MillePoels/MurPhySDR/hardware/kicad/AD9364_IO.kicad_sch

## KiCad design hardware/kicad/AD9364_IO.kicad_sch (2024-05-19)

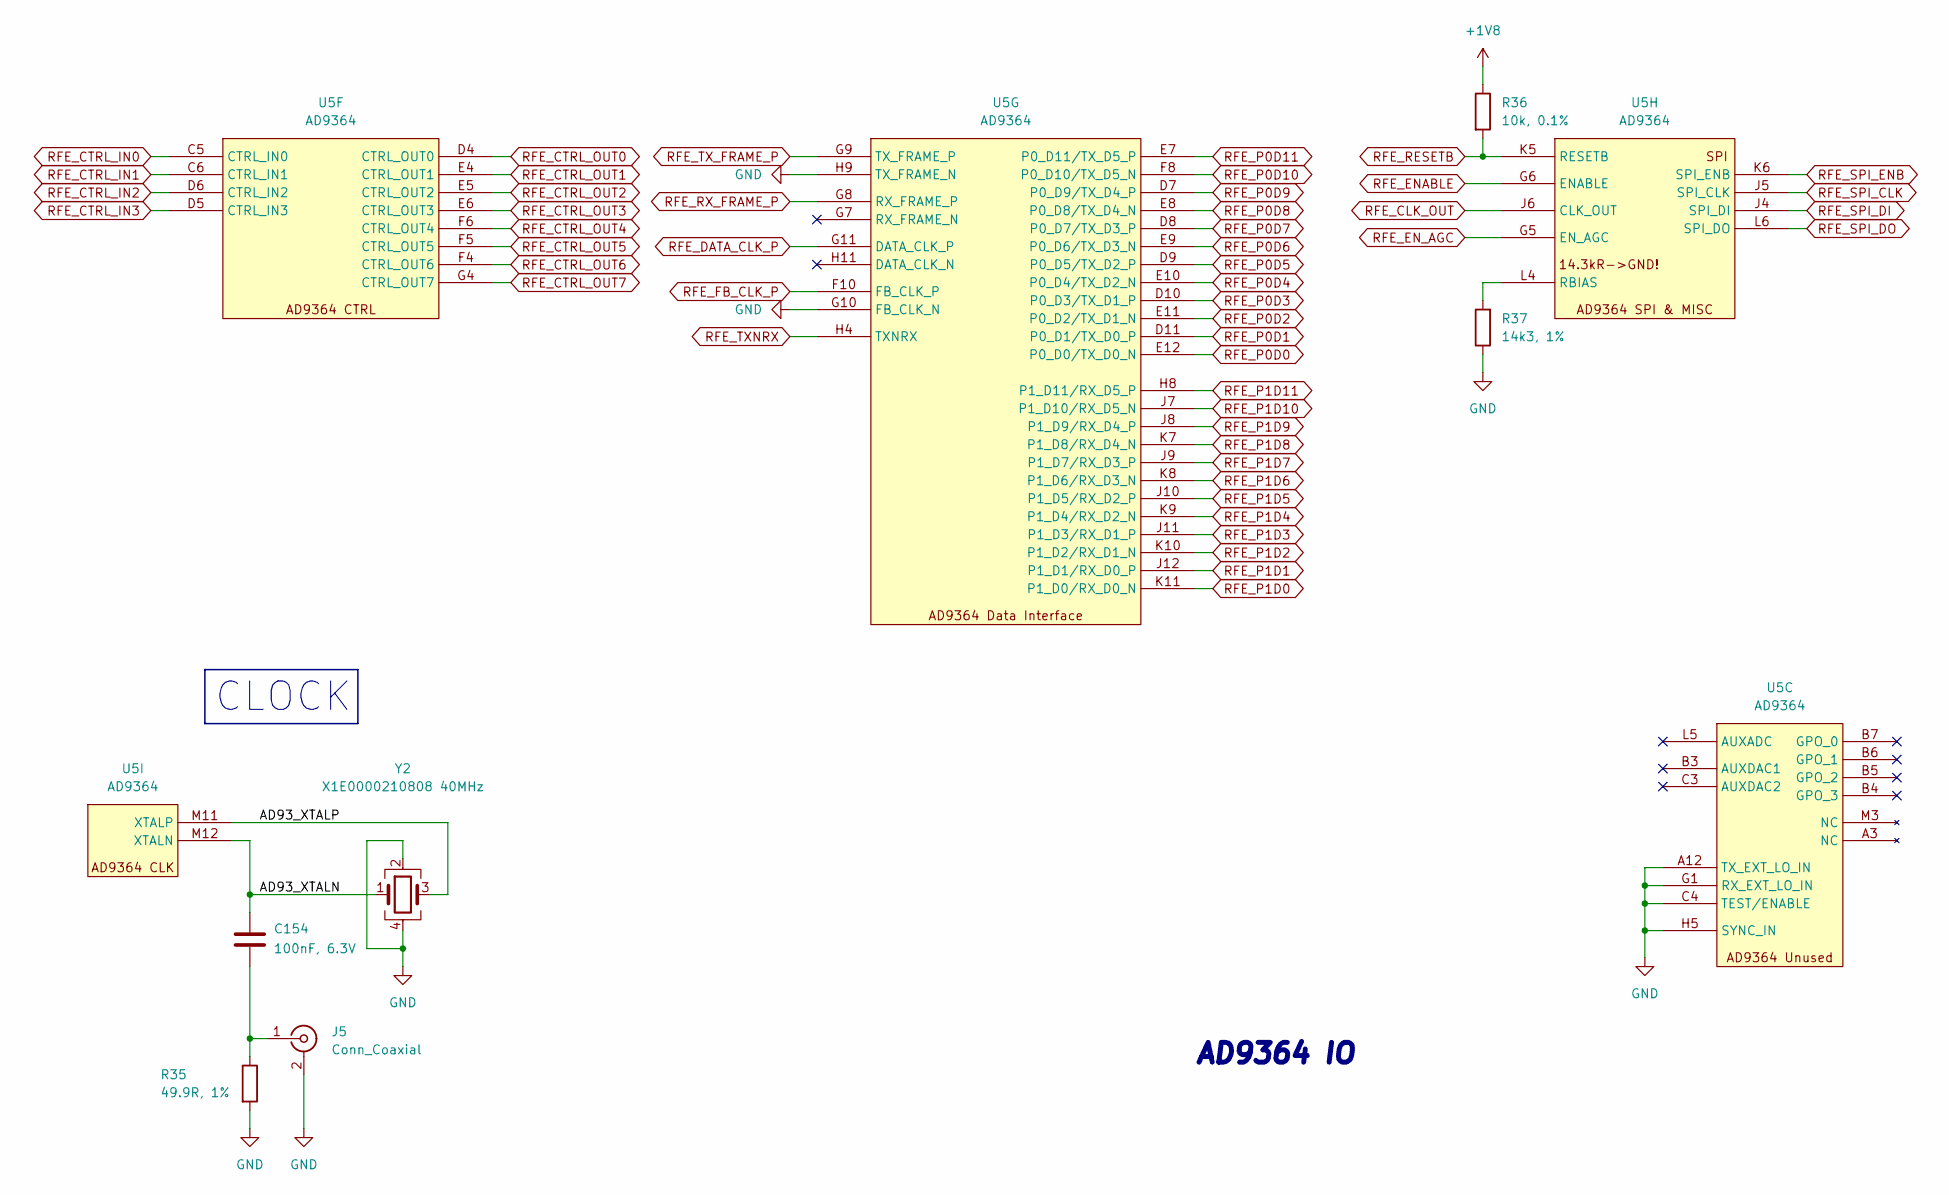
[picture p35: schematic AD9364_IO.kicad_sch]

Parts:
C154: 100nF, 6.3V; C_0201_0603Metric; Manufacturer_Part_Number GRM033R60J104KE19D; Mouser Part Number 81-GRM033R60J104KE19
J5: Conn_Coaxial; SMA_Molex_73251-1153_EdgeMount_Horizontal; Manufacturer_Part_Number 0732511150; Mouser Part Number 538-73251-1150
R35: 49.9R, 1%; R_0402_1005Metric; Manufacturer_Part_Number RC0402FR-0749R9L; Mouser Part Number 603-RC0402FR-0749R9L
R36: 10k, 0.1%; R_0402_1005Metric; Manufacturer_Part_Number RT0402BRD0710KL; Mouser Part Number 603-RT0402BRD0710KL
R37: 14k3, 1%; R_0402_1005Metric; Manufacturer_Part_Number RC0402FR-0714K3L; Mouser Part Number 603-RC0402FR-0714K3L
U5: AD9364; Manufacturer_Part_Number AD9364BBCZ; Mouser Part Number 584-AD9364BBCZ
Y2: X1E0000210808 40MHz; Crystal_SMD_SeikoEpson_TSX3225-4Pin_3.2x2.5mm; Manufacturer_Part_Number X1E0000210808; Mouser Part Number /

Connections:
+1V8: R36.1
AD93_XTALN: C154.1, U5.M12 (XTALN), Y2.1
AD93_XTALP: U5.M11 (XTALP), Y2.3
GND: J5.2 (Ext), R35.2, R37.1, U5.A12 (TX_EXT_LO_IN), U5.C4 (TEST/ENABLE), U5.G1 (RX_EXT_LO_IN), U5.G10 (FB_CLK_N), U5.H5 (SYNC_IN), U5.H9 (TX_FRAME_N), Y2.2, Y2.4
unnamed: C154.2, J5.1 (In), R35.1
unnamed: R37.2, U5.L4 (RBIAS)
RFE_CLK_OUT: U5.J6 (CLK_OUT)
RFE_CTRL_IN0: U5.C5 (CTRL_IN0)
RFE_CTRL_IN1: U5.C6 (CTRL_IN1)
RFE_CTRL_IN2: U5.D6 (CTRL_IN2)
RFE_CTRL_IN3: U5.D5 (CTRL_IN3)
RFE_CTRL_OUT0: U5.D4 (CTRL_OUT0)
RFE_CTRL_OUT1: U5.E4 (CTRL_OUT1)
RFE_CTRL_OUT2: U5.E5 (CTRL_OUT2)
RFE_CTRL_OUT3: U5.E6 (CTRL_OUT3)
RFE_CTRL_OUT4: U5.F6 (CTRL_OUT4)
RFE_CTRL_OUT5: U5.F5 (CTRL_OUT5)
RFE_CTRL_OUT6: U5.F4 (CTRL_OUT6)
RFE_CTRL_OUT7: U5.G4 (CTRL_OUT7)
RFE_DATA_CLK_P: U5.G11 (DATA_CLK_P)
RFE_ENABLE: U5.G6 (ENABLE)
RFE_EN_AGC: U5.G5 (EN_AGC)
RFE_FB_CLK_P: U5.F10 (FB_CLK_P)
RFE_P0D0: U5.E12 (P0_D0/TX_D0_N)
RFE_P0D1: U5.D11 (P0_D1/TX_D0_P)
RFE_P0D2: U5.E11 (P0_D2/TX_D1_N)
RFE_P0D3: U5.D10 (P0_D3/TX_D1_P)
RFE_P0D4: U5.E10 (P0_D4/TX_D2_N)
RFE_P0D5: U5.D9 (P0_D5/TX_D2_P)
RFE_P0D6: U5.E9 (P0_D6/TX_D3_N)
RFE_P0D7: U5.D8 (P0_D7/TX_D3_P)
RFE_P0D8: U5.E8 (P0_D8/TX_D4_N)
RFE_P0D9: U5.D7 (P0_D9/TX_D4_P)
RFE_P0D10: U5.F8 (P0_D10/TX_D5_N)
RFE_P0D11: U5.E7 (P0_D11/TX_D5_P)
RFE_P1D0: U5.K11 (P1_D0/RX_D0_N)
RFE_P1D1: U5.J12 (P1_D1/RX_D0_P)
RFE_P1D2: U5.K10 (P1_D2/RX_D1_N)
RFE_P1D3: U5.J11 (P1_D3/RX_D1_P)
RFE_P1D4: U5.K9 (P1_D4/RX_D2_N)
RFE_P1D5: U5.J10 (P1_D5/RX_D2_P)
RFE_P1D6: U5.K8 (P1_D6/RX_D3_N)
RFE_P1D7: U5.J9 (P1_D7/RX_D3_P)
RFE_P1D8: U5.K7 (P1_D8/RX_D4_N)
RFE_P1D9: U5.J8 (P1_D9/RX_D4_P)
RFE_P1D10: U5.J7 (P1_D10/RX_D5_N)
RFE_P1D11: U5.H8 (P1_D11/RX_D5_P)
RFE_RESETB: R36.2, U5.K5 (RESETB)
RFE_RX_FRAME_P: U5.G8 (RX_FRAME_P)
RFE_SPI_CLK: U5.J5 (SPI_CLK)
RFE_SPI_DI: U5.J4 (SPI_DI)
RFE_SPI_DO: U5.L6 (SPI_DO)
RFE_SPI_ENB: U5.K6 (SPI_ENB)
RFE_TXNRX: U5.H4 (TXNRX)
RFE_TX_FRAME_P: U5.G9 (TX_FRAME_P)

Notes on the sheet:
AD9364 IO
CLOCK
