MillePoels/MurPhySDR/hardware/kicad/AD9364_RF.kicad_sch

## KiCad design hardware/kicad/AD9364_RF.kicad_sch (2024-05-19)

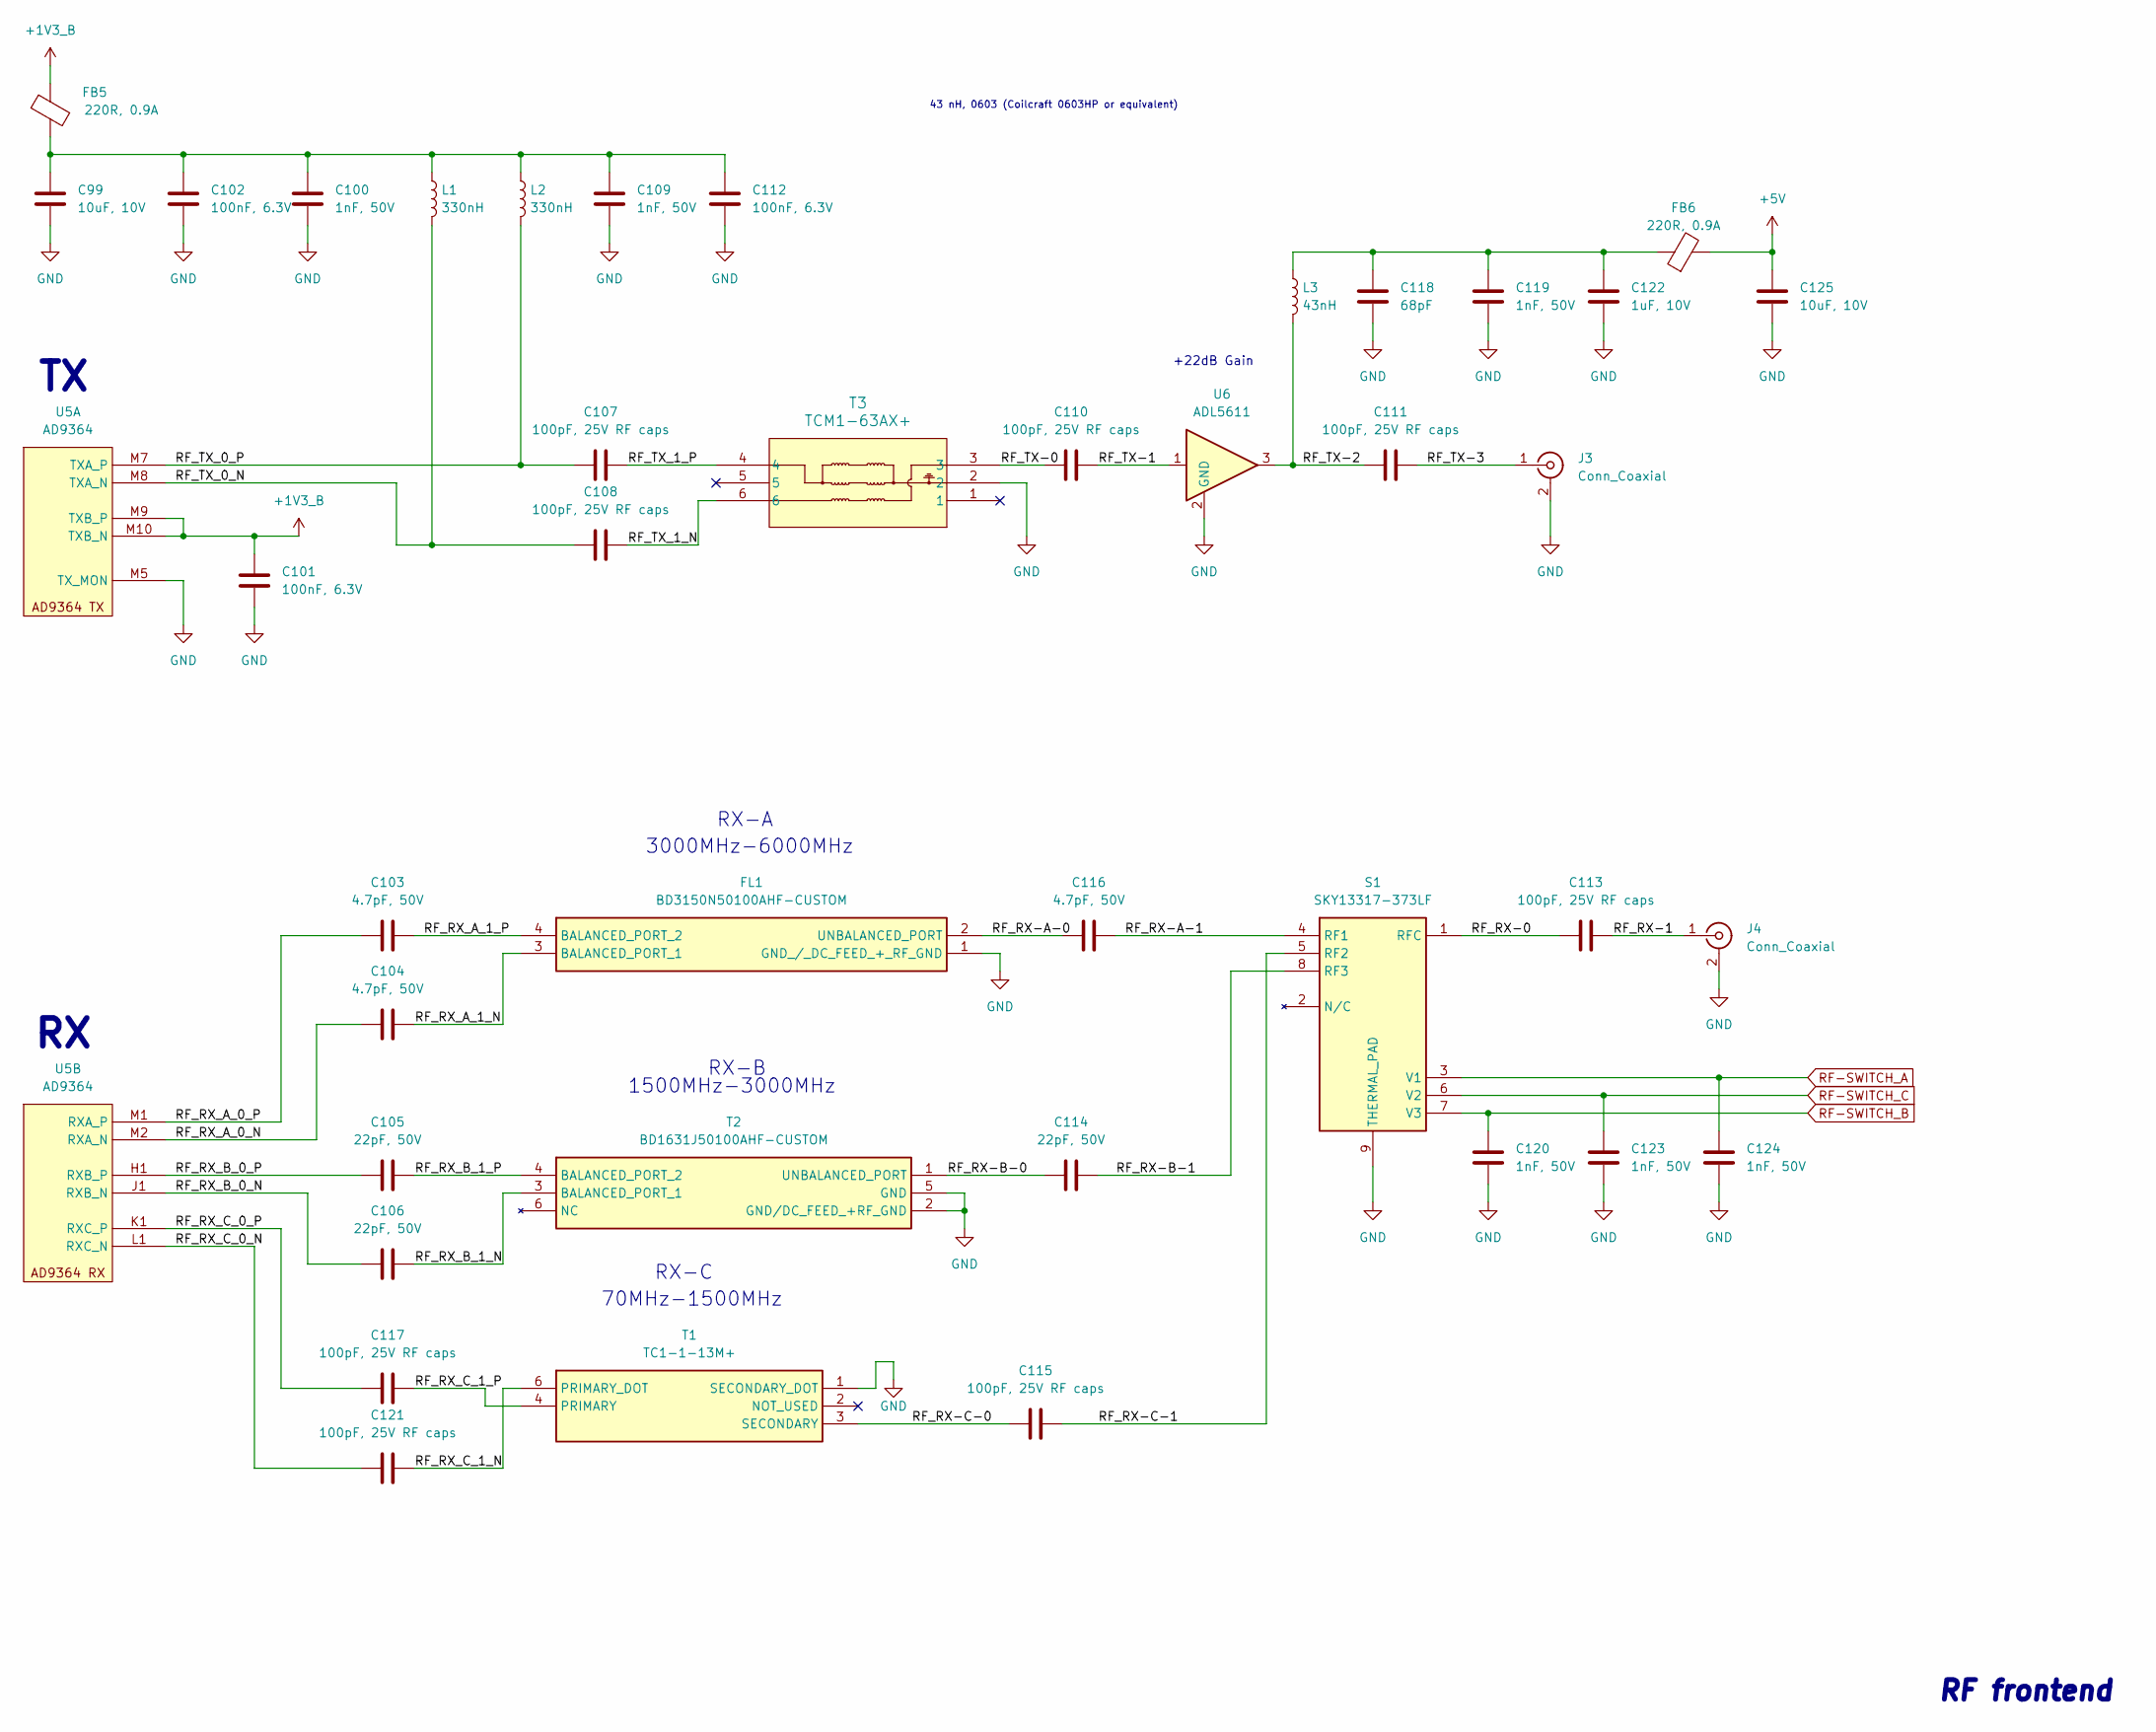
[picture p36: schematic AD9364_RF.kicad_sch]

Parts:
C99, C125: 10uF, 10V; C_0603_1608Metric; Manufacturer_Part_Number GRM188R61A106ME69D; Mouser Part Number 81-GRM188R61A106ME9D
C100, C109, C119, C120, C123, C124: 1nF, 50V; C_0201_0603Metric; Manufacturer_Part_Number GRM0335C1H102JE01D; Mouser Part Number 81-GRM0335C1H102JE1D
C101, C102, C112: 100nF, 6.3V; C_0201_0603Metric; Manufacturer_Part_Number GRM033R60J104KE19D; Mouser Part Number 81-GRM033R60J104KE19
C103, C104, C116: 4.7pF, 50V; C_0201_0603Metric; Manufacturer_Part_Number GRM0335C1H4R7BA01D; Mouser Part Number 81-GRM0335C1H4R7BA1D
C105, C106, C114: 22pF, 50V; C_0201_0603Metric; Manufacturer_Part_Number GRM0335C1H220JA01D; Mouser Part Number 81-GRM0335C1H220JA1D
C107, C108, C110, C111, C113, C115, C117, C121: 100pF, 25V RF caps; C_0402_1005Metric; Manufacturer_Part_Number CBR04C101G3GAC; Mouser Part Number 80-CBR04C101G3GAC
C118: 68pF; C_0402_1005Metric; Manufacturer_Part_Number CC0402JRNPO9BN680; Mouser Part Number 603-CC402JRNPO9BN680
C122: 1uF, 10V; C_0402_1005Metric; Manufacturer_Part_Number GRM155Z71A105KE01D; Mouser Part Number 81-GRM155Z71A105KE1D
FB5, FB6: 220R, 0.9A; L_0402_1005Metric; Manufacturer_Part_Number MPZ1005S221ET000; Mouser Part Number 810-MPZ1005S221ET000
FL1: BD3150N50100AHF-CUSTOM; BD3150N50100AHF; Mouser Part Number 620-BD3150N50100AHF
J3, J4: Conn_Coaxial; SMA_Molex_73251-1153_EdgeMount_Horizontal; Manufacturer_Part_Number 0732511150; Mouser Part Number 538-73251-1150
L1, L2: 330nH; L_0402_1005Metric; Manufacturer_Part_Number LQW15CNR33J1ZD; Mouser Part Number 81-LQW15CNR33J1ZD
L3: 43nH; L_0603_1608Metric; Manufacturer_Part_Number LQW18AN43NG00D; Mouser Part Number 81-LQW18AN43NG00D
S1: SKY13317-373LF; SON40P155X155X50-9N_(SKY13317-373LF); Mouser Part Number 873-SKY13317-373LF
T1: TC1-1-13M+; TC1113MA; Mouser Part Number 139-TC1-1-13MA
T2: BD1631J50100AHF-CUSTOM; BD1631J50100AHF; Mouser Part Number 620-BD1631J50100AHF
T3: TCM1-63AX+; Manufacturer_Part_Number TCM1-63AX+; Mouser Part Number 139-TCM1-63AX
U5: AD9364; Manufacturer_Part_Number AD9364BBCZ; Mouser Part Number 584-AD9364BBCZ
U6: ADL5611; SOT-89-3; Manufacturer_Part_Number ADL5611ARKZ-R7; Mouser Part Number ADL5611ARKZ-R7

Connections:
+1V3_B: C101.1, FB5.2, U5.M9 (TXB_P), U5.M10 (TXB_N)
+5V: C125.1, FB6.2
GND: C99.2, C100.2, C101.2, C102.2, C109.2, C112.2, C118.2, C119.2, C120.2, C122.1, C123.2, C124.2, C125.2, FL1.1 (GND_/_DC_FEED_+_RF_GND), J3.2 (Ext), J4.2 (Ext), S1.9 (THERMAL_PAD), T1.1 (SECONDARY_DOT), T2.2 (GND/DC_FEED_+RF_GND), T2.5 (GND), T3.2, U5.M5 (TX_MON), U6.2 (GND)
unnamed: C99.1, C100.1, C102.1, C109.1, C112.1, FB5.1, L1.1, L2.1
unnamed: C118.1, C119.1, C122.2, FB6.1, L3.1
RF-SWITCH_A: C124.1, S1.3 (V1)
RF-SWITCH_B: C120.1, S1.7 (V3)
RF-SWITCH_C: C123.1, S1.6 (V2)
RF_RX-0: C113.1, S1.1 (RFC)
RF_RX-1: C113.2, J4.1 (In)
RF_RX-A-0: C116.1, FL1.2 (UNBALANCED_PORT)
RF_RX-A-1: C116.2, S1.4 (RF1)
RF_RX-B-0: C114.1, T2.1 (UNBALANCED_PORT)
RF_RX-B-1: C114.2, S1.8 (RF3)
RF_RX-C-0: C115.1, T1.3 (SECONDARY)
RF_RX-C-1: C115.2, S1.5 (RF2)
RF_RX_A_0_N: C104.1, U5.M2 (RXA_N)
RF_RX_A_0_P: C103.1, U5.M1 (RXA_P)
RF_RX_A_1_N: C104.2, FL1.3 (BALANCED_PORT_1)
RF_RX_A_1_P: C103.2, FL1.4 (BALANCED_PORT_2)
RF_RX_B_0_N: C106.1, U5.J1 (RXB_N)
RF_RX_B_0_P: C105.1, U5.H1 (RXB_P)
RF_RX_B_1_N: C106.2, T2.3 (BALANCED_PORT_1)
RF_RX_B_1_P: C105.2, T2.4 (BALANCED_PORT_2)
RF_RX_C_0_N: C121.1, U5.L1 (RXC_N)
RF_RX_C_0_P: C117.1, U5.K1 (RXC_P)
RF_RX_C_1_N: C121.2, T1.6 (PRIMARY_DOT)
RF_RX_C_1_P: C117.2, T1.4 (PRIMARY)
RF_TX-0: C110.1, T3.3
RF_TX-1: C110.2, U6.1
RF_TX-2: C111.1, L3.2, U6.3
RF_TX-3: C111.2, J3.1 (In)
RF_TX_0_N: C108.1, L1.2, U5.M8 (TXA_N)
RF_TX_0_P: C107.1, L2.2, U5.M7 (TXA_P)
RF_TX_1_N: C108.2, T3.6
RF_TX_1_P: C107.2, T3.4

Notes on the sheet:
43 nH, 0603 (Coilcraft 0603HP or equivalent)
RF frontend
RX-C
+22dB Gain
3000MHz-6000MHz
1500MHz-3000MHz
RX-B
RX-A
70MHz-1500MHz
