MillePoels/MurPhySDR/hardware/kicad/AD9364_power-supply.kicad_sch

## KiCad design hardware/kicad/AD9364_power-supply.kicad_sch (2024-05-19)

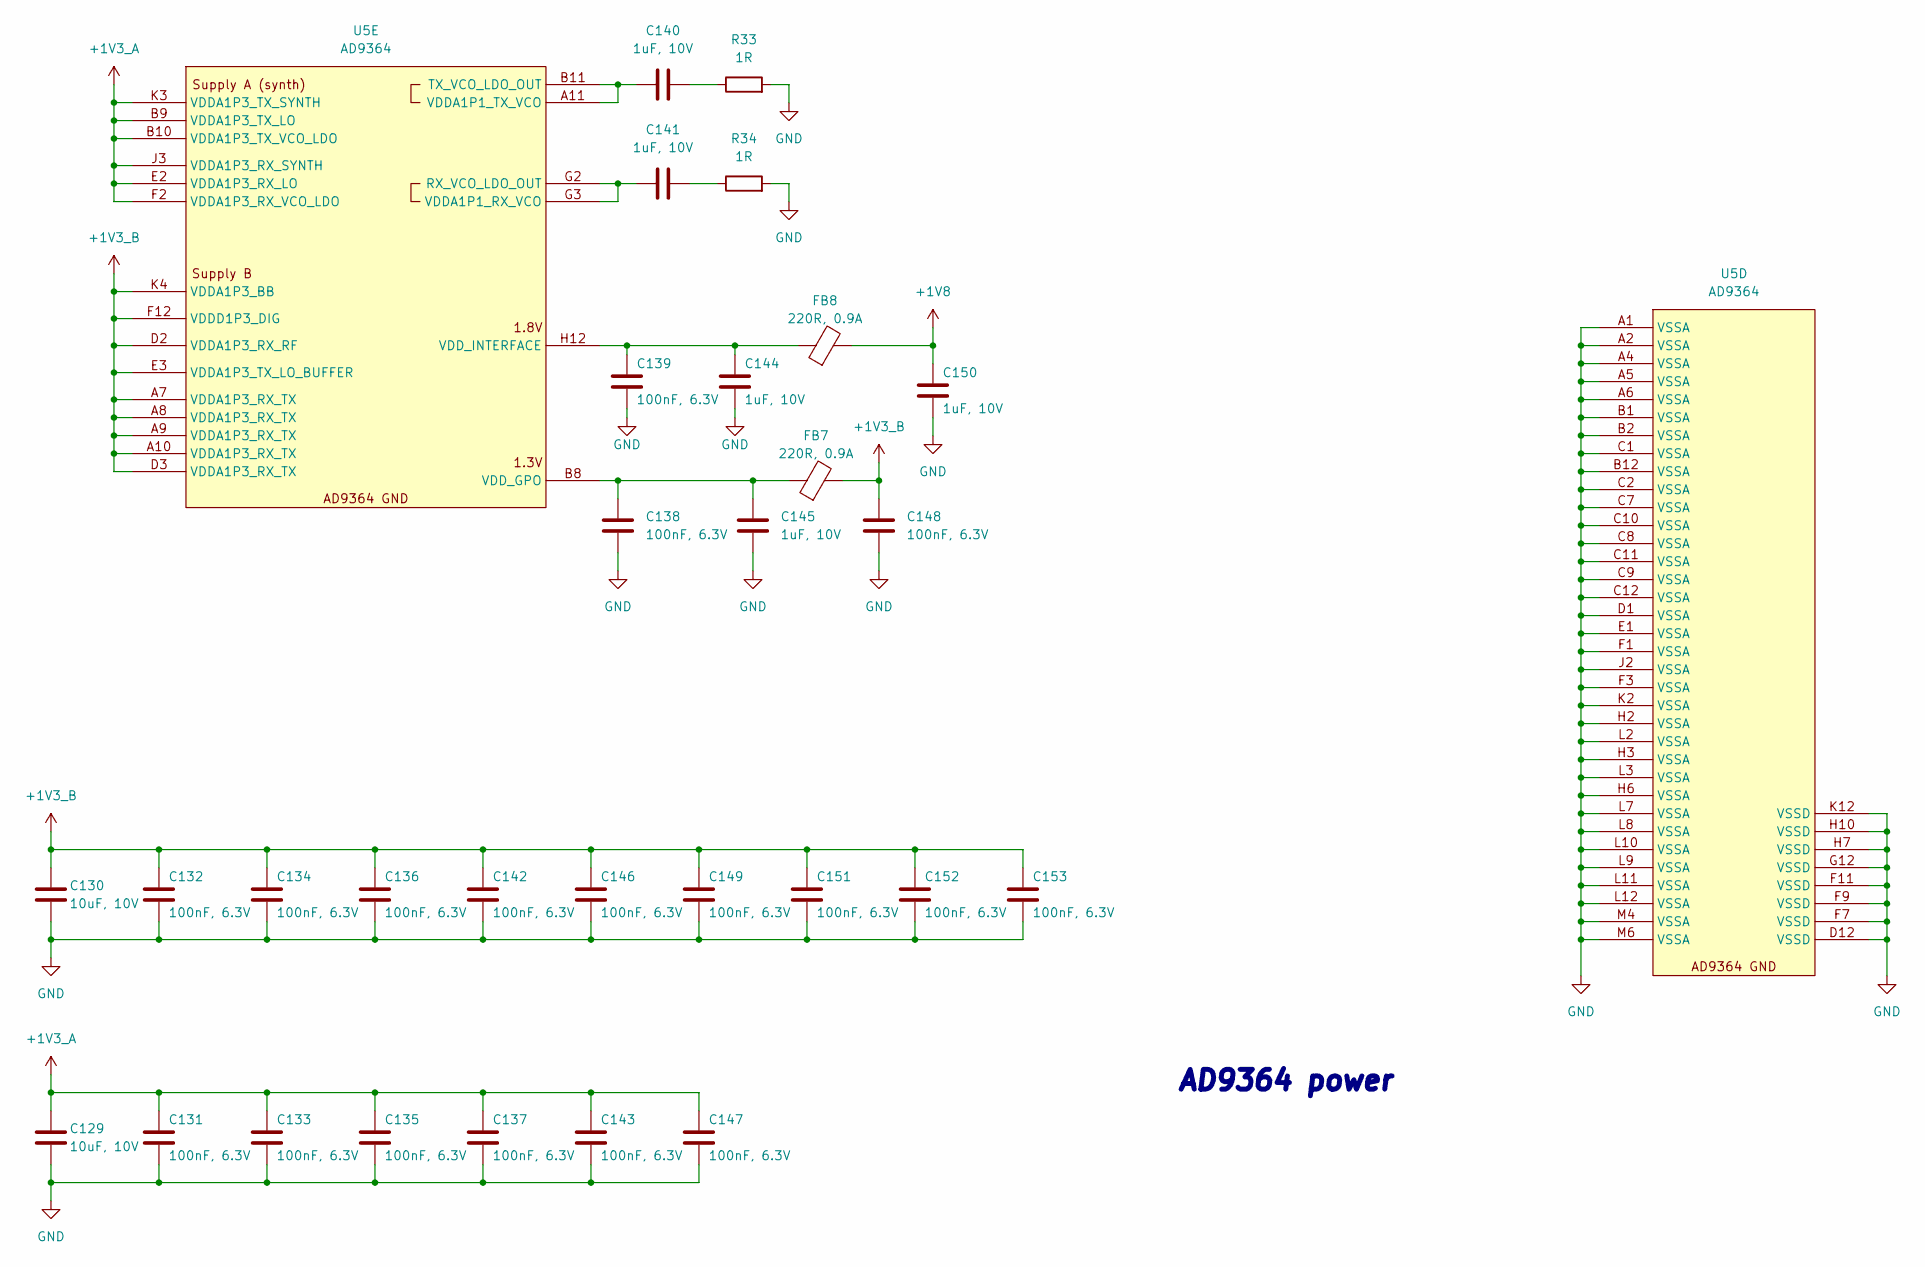
[picture p37: schematic AD9364_power-supply.kicad_sch]

Parts:
C129, C130: 10uF, 10V; C_0603_1608Metric; Manufacturer_Part_Number GRM188R61A106ME69D; Mouser Part Number 81-GRM188R61A106ME9D
C131, C132, C133, C134, C135, C136, C137, C138, C139, C142, C143, C146, C147, C148, C149, C151, C152, C153: 100nF, 6.3V; C_0201_0603Metric; Manufacturer_Part_Number GRM033R60J104KE19D; Mouser Part Number 81-GRM033R60J104KE19
C140, C141, C144, C145, C150: 1uF, 10V; C_0402_1005Metric; Manufacturer_Part_Number GRM155Z71A105KE01D; Mouser Part Number 81-GRM155Z71A105KE1D
FB7, FB8: 220R, 0.9A; L_0402_1005Metric; Manufacturer_Part_Number MPZ1005S221ET000; Mouser Part Number 810-MPZ1005S221ET000
R33, R34: 1R; R_0402_1005Metric; Manufacturer_Part_Number RC0402FR-071RL; Mouser Part Number 603-RC0402FR-071RL
U5: AD9364; Manufacturer_Part_Number AD9364BBCZ; Mouser Part Number 584-AD9364BBCZ

Connections:
+1V3_A: C129.1, C131.1, C133.1, C135.1, C137.1, C143.1, C147.1, U5.B9 (VDDA1P3_TX_LO), U5.B10 (VDDA1P3_TX_VCO_LDO), U5.E2 (VDDA1P3_RX_LO), U5.F2 (VDDA1P3_RX_VCO_LDO), U5.J3 (VDDA1P3_RX_SYNTH), U5.K3 (VDDA1P3_TX_SYNTH)
+1V3_B: C130.1, C132.1, C134.1, C136.1, C142.1, C146.1, C148.1, C149.1, C151.1, C152.1, C153.1, FB7.2, U5.A7 (VDDA1P3_RX_TX), U5.A8 (VDDA1P3_RX_TX), U5.A9 (VDDA1P3_RX_TX), U5.A10 (VDDA1P3_RX_TX), U5.D2 (VDDA1P3_RX_RF), U5.D3 (VDDA1P3_RX_TX), U5.E3 (VDDA1P3_TX_LO_BUFFER), U5.F12 (VDDD1P3_DIG), U5.K4 (VDDA1P3_BB)
+1V8: C150.1, FB8.2
GND: C129.2, C130.2, C131.2, C132.2, C133.2, C134.2, C135.2, C136.2, C137.2, C138.2, C139.2, C142.2, C143.2, C144.2, C145.2, C146.2, C147.2, C148.2, C149.2, C150.2, C151.2, C152.2, C153.2, R33.2, R34.2, U5.A1 (VSSA), U5.A2 (VSSA), U5.A4 (VSSA), U5.A5 (VSSA), U5.A6 (VSSA), U5.B1 (VSSA), U5.B2 (VSSA), U5.B12 (VSSA), U5.C1 (VSSA), U5.C2 (VSSA), U5.C7 (VSSA), U5.C8 (VSSA), U5.C9 (VSSA), U5.C10 (VSSA), U5.C11 (VSSA), U5.C12 (VSSA), U5.D1 (VSSA), U5.D12 (VSSD), U5.E1 (VSSA), U5.F1 (VSSA), U5.F3 (VSSA), U5.F7 (VSSD), U5.F9 (VSSD), U5.F11 (VSSD), U5.G12 (VSSD), U5.H2 (VSSA), U5.H3 (VSSA), U5.H6 (VSSA), U5.H7 (VSSD), U5.H10 (VSSD), U5.J2 (VSSA), U5.K2 (VSSA), U5.K12 (VSSD), U5.L2 (VSSA), U5.L3 (VSSA), U5.L7 (VSSA), U5.L8 (VSSA), U5.L9 (VSSA), U5.L10 (VSSA), U5.L11 (VSSA), U5.L12 (VSSA), U5.M4 (VSSA), U5.M6 (VSSA)
unnamed: C138.1, C145.1, FB7.1, U5.B8 (VDD_GPO)
unnamed: C139.1, C144.1, FB8.1, U5.H12 (VDD_INTERFACE)
unnamed: C140.1, R33.1
unnamed: C140.2, U5.A11 (VDDA1P1_TX_VCO), U5.B11 (TX_VCO_LDO_OUT)
unnamed: C141.1, R34.1
unnamed: C141.2, U5.G2 (RX_VCO_LDO_OUT), U5.G3 (VDDA1P1_RX_VCO)

Notes on the sheet:
AD9364 power
