MillePoels/MurPhySDR/hardware/kicad/FT601Q.kicad_sch

## KiCad design hardware/kicad/FT601Q.kicad_sch (2024-05-19)

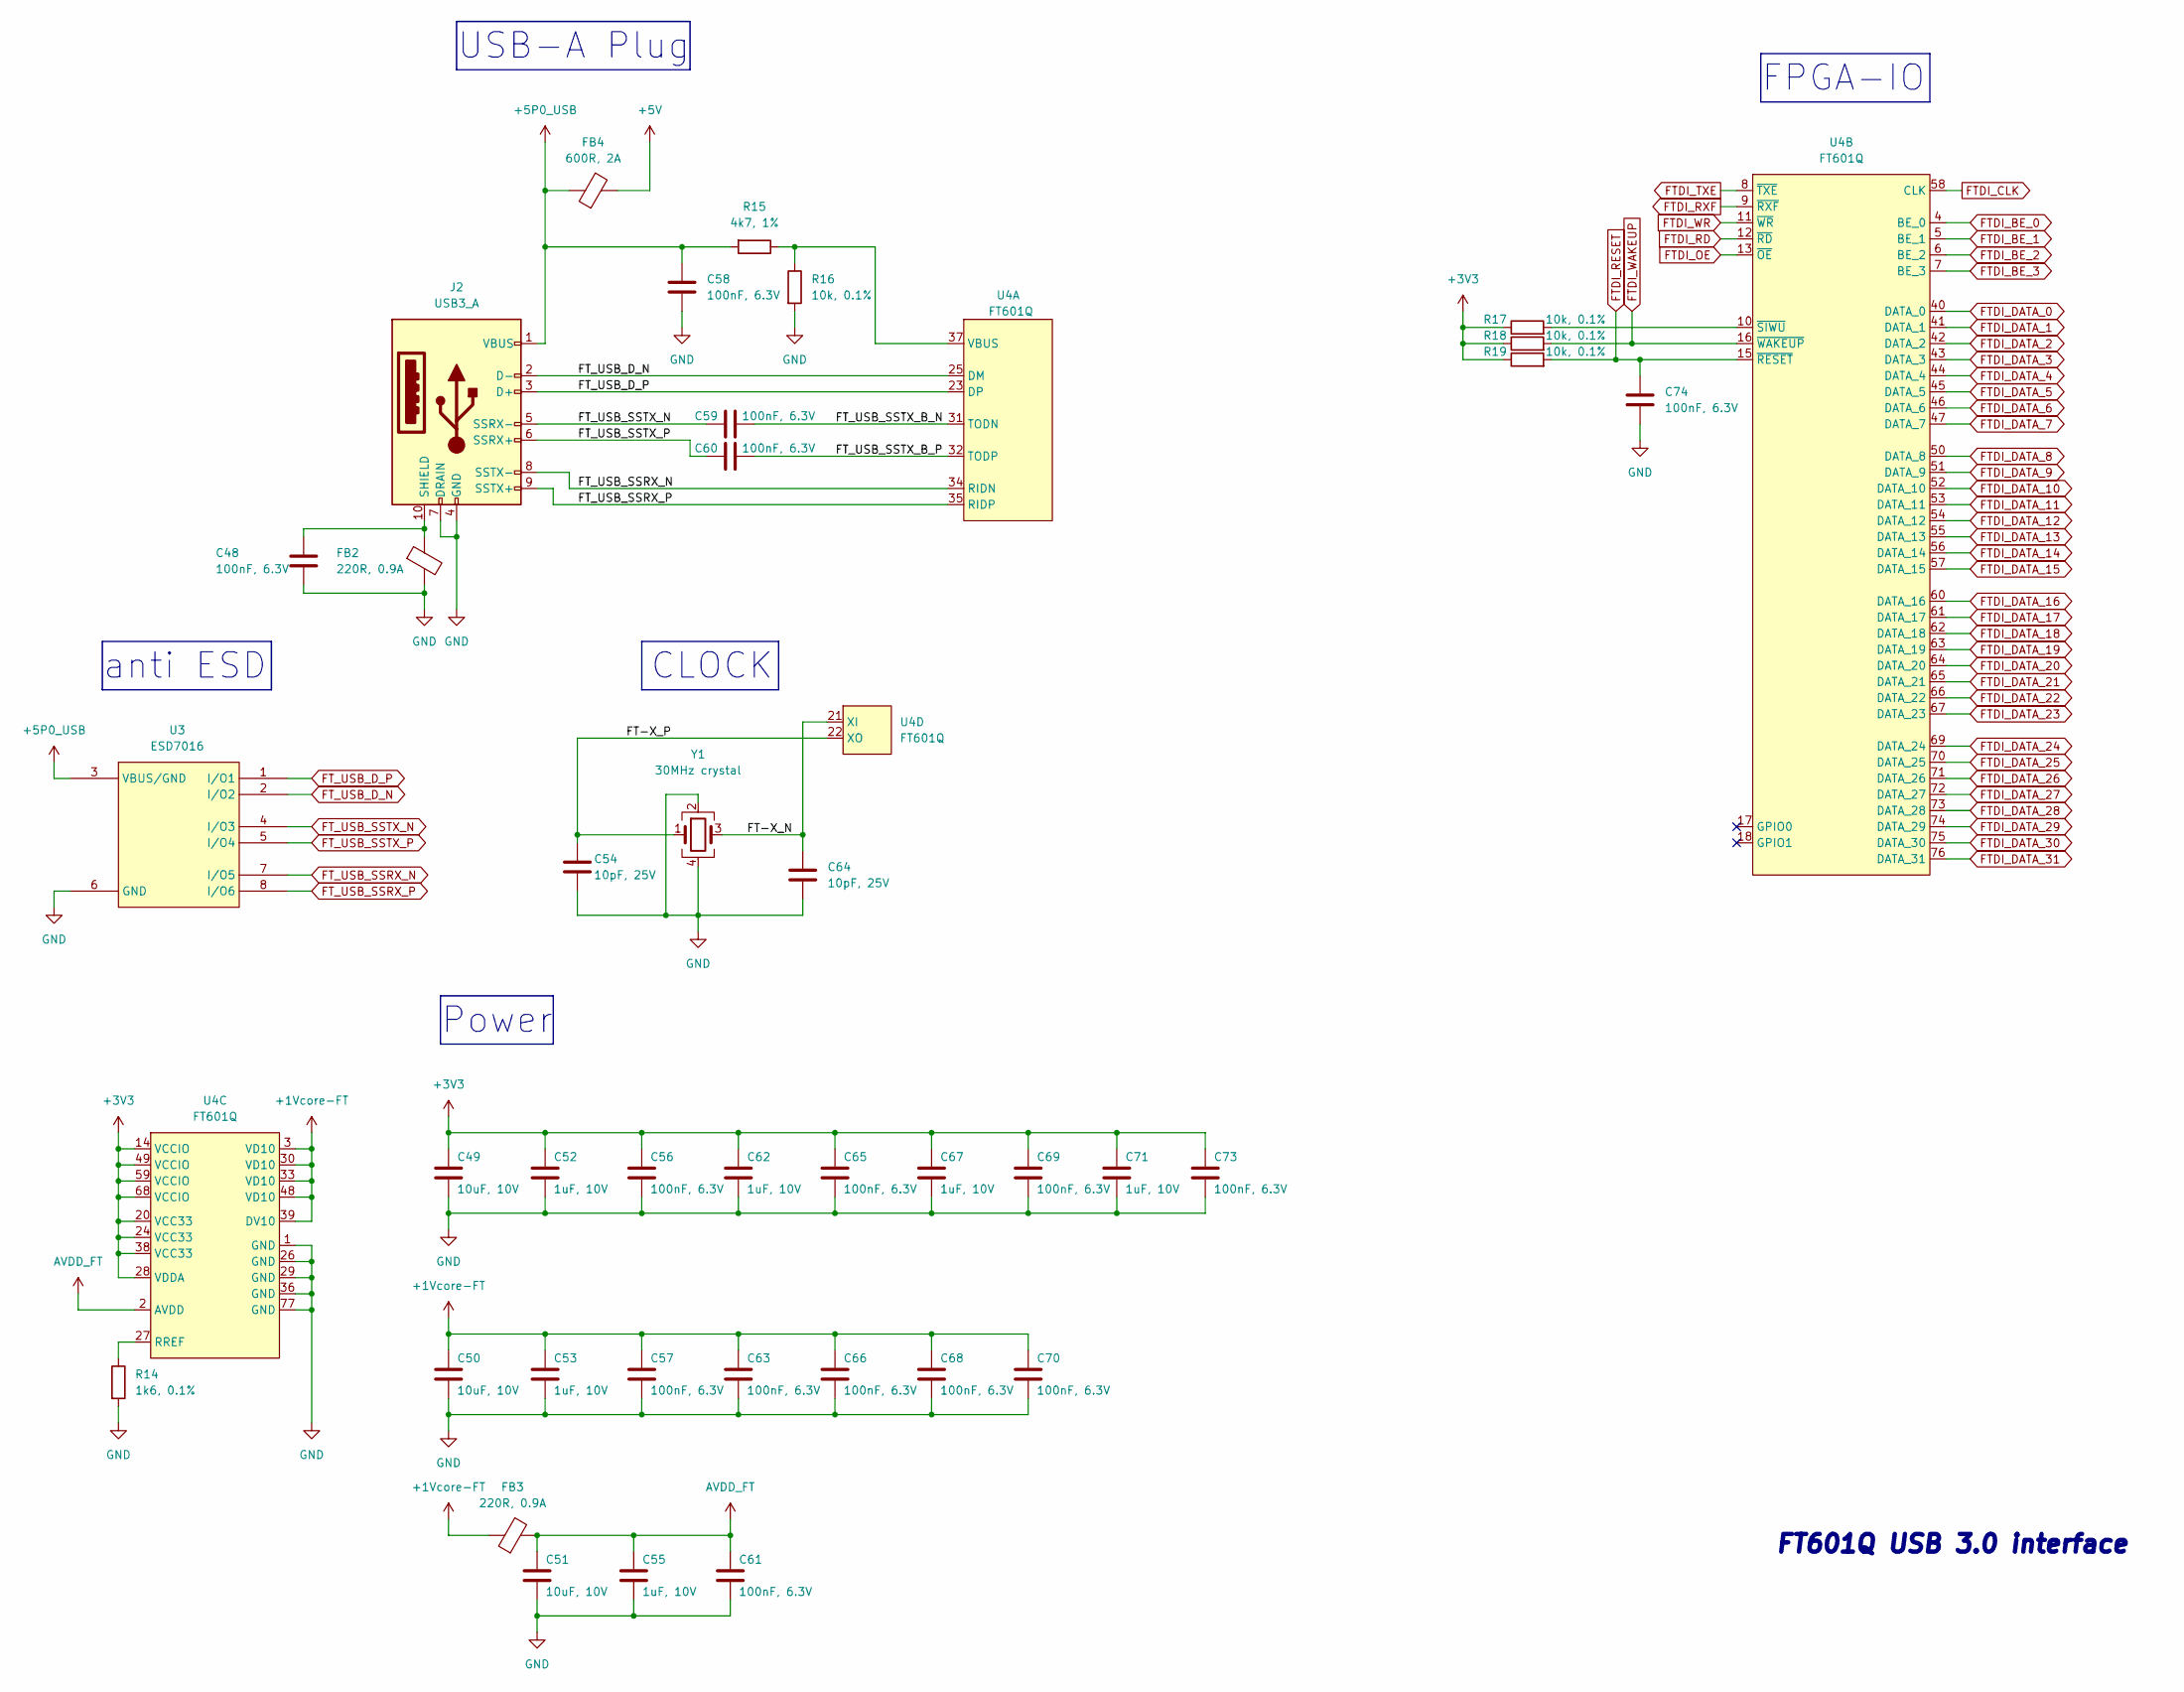
[picture p38: schematic FT601Q.kicad_sch]

Parts:
C48, C56, C57, C58, C59, C60, C61, C63, C65, C66, C68, C69, C70, C73, C74: 100nF, 6.3V; C_0201_0603Metric; Manufacturer_Part_Number GRM033R60J104KE19D; Mouser Part Number 81-GRM033R60J104KE19
C49, C50, C51: 10uF, 10V; C_0603_1608Metric; Manufacturer_Part_Number GRM188R61A106ME69D; Mouser Part Number 81-GRM188R61A106ME9D
C52, C53, C55, C62, C67, C71: 1uF, 10V; C_0402_1005Metric; Manufacturer_Part_Number GRM155Z71A105KE01D; Mouser Part Number 81-GRM155Z71A105KE1D
C54, C64: 10pF, 25V; C_0402_1005Metric; Manufacturer_Part_Number GRM1555C1E100JA01D; Mouser Part Number 81-GRM1555C1E100JA1D
FB2, FB3: 220R, 0.9A; L_0402_1005Metric; Manufacturer_Part_Number MPZ1005S221ET000; Mouser Part Number 810-MPZ1005S221ET000
FB4: 600R, 2A; L_0805_2012Metric; Manufacturer_Part_Number MPZ2012S601AT000; Mouser Part Number 810-MPZ2012S601AT000
J2: USB3_A; USB3.0-A-SMD_U237-091N-4BLVS10-1; Manufacturer_Part_Number U237-091N-4BLVS10-1; Mouser Part Number /
R14: 1k6, 0.1%; R_0402_1005Metric; Manufacturer_Part_Number RT0402BRD071K6L; Mouser Part Number 603-RT0402BRD071K6L
R15: 4k7, 1%; R_0402_1005Metric; Manufacturer_Part_Number RC0402FR-074K7L; Mouser Part Number 603-RC0402FR-074K7L
R16, R17, R18, R19: 10k, 0.1%; R_0402_1005Metric; Manufacturer_Part_Number RT0402BRD0710KL; Mouser Part Number 603-RT0402BRD0710KL
U3: ESD7016; UDFN8_3P3X1_517CB_ONS; Manufacturer_Part_Number ESD7016MUTAG; Mouser Part Number 863-ESD7016MUTAG
U4: FT601Q; QFN-76-1EP_9x9mm_P0.4mm_EP5.81x6.31mm; Manufacturer_Part_Number FT601Q-B-T; Mouser Part Number 895-FT601Q-B-T
Y1: 30MHz crystal; Crystal_SMD_3225-4Pin_3.2x2.5mm; Manufacturer_Part_Number CX3225SB30000D0FPLCC; Mouser Part Number 581-CX3225SB3DFPLCC

Connections:
+1Vcore-FT: C50.1, C53.1, C57.1, C63.1, C66.1, C68.1, C70.1, FB3.1, U4.3 (VD10), U4.30 (VD10), U4.33 (VD10), U4.39 (DV10), U4.48 (VD10)
+3V3: C49.1, C52.1, C56.1, C62.1, C65.1, C67.1, C69.1, C71.1, C73.1, R17.1, R18.1, R19.1, U4.14 (VCCIO), U4.20 (VCC33), U4.24 (VCC33), U4.28 (VDDA), U4.38 (VCC33), U4.49 (VCCIO), U4.59 (VCCIO), U4.68 (VCCIO)
+5P0_USB: C58.1, FB4.1, J2.1 (VBUS), R15.2, U3.3 (VBUS/GND)
+5V: FB4.2
AVDD_FT: C51.1, C55.1, C61.1, FB3.2, U4.2 (AVDD)
FT-X_N: C64.1, U4.21 (XI), Y1.3
FT-X_P: C54.1, U4.22 (XO), Y1.1
FTDI_BE_0: U4.4 (BE_0)
FTDI_BE_1: U4.5 (BE_1)
FTDI_BE_2: U4.6 (BE_2)
FTDI_BE_3: U4.7 (BE_3)
FTDI_CLK: U4.58 (CLK)
FTDI_DATA_0: U4.40 (DATA_0)
FTDI_DATA_1: U4.41 (DATA_1)
FTDI_DATA_2: U4.42 (DATA_2)
FTDI_DATA_3: U4.43 (DATA_3)
FTDI_DATA_4: U4.44 (DATA_4)
FTDI_DATA_5: U4.45 (DATA_5)
FTDI_DATA_6: U4.46 (DATA_6)
FTDI_DATA_7: U4.47 (DATA_7)
FTDI_DATA_8: U4.50 (DATA_8)
FTDI_DATA_9: U4.51 (DATA_9)
FTDI_DATA_10: U4.52 (DATA_10)
FTDI_DATA_11: U4.53 (DATA_11)
FTDI_DATA_12: U4.54 (DATA_12)
FTDI_DATA_13: U4.55 (DATA_13)
FTDI_DATA_14: U4.56 (DATA_14)
FTDI_DATA_15: U4.57 (DATA_15)
FTDI_DATA_16: U4.60 (DATA_16)
FTDI_DATA_17: U4.61 (DATA_17)
FTDI_DATA_18: U4.62 (DATA_18)
FTDI_DATA_19: U4.63 (DATA_19)
FTDI_DATA_20: U4.64 (DATA_20)
FTDI_DATA_21: U4.65 (DATA_21)
FTDI_DATA_22: U4.66 (DATA_22)
FTDI_DATA_23: U4.67 (DATA_23)
FTDI_DATA_24: U4.69 (DATA_24)
FTDI_DATA_25: U4.70 (DATA_25)
FTDI_DATA_26: U4.71 (DATA_26)
FTDI_DATA_27: U4.72 (DATA_27)
FTDI_DATA_28: U4.73 (DATA_28)
FTDI_DATA_29: U4.74 (DATA_29)
FTDI_DATA_30: U4.75 (DATA_30)
FTDI_DATA_31: U4.76 (DATA_31)
FTDI_OE: U4.13 (~OE)
FTDI_RD: U4.12 (~RD)
FTDI_RESET: C74.1, R19.2, U4.15 (~RESET)
FTDI_RXF: U4.9 (~RXF)
FTDI_TXE: U4.8 (~TXE)
FTDI_WAKEUP: R18.2, U4.16 (~WAKEUP)
FTDI_WR: U4.11 (~WR)
FT_USB_D_N: J2.2 (D-), U3.2 (I/O2), U4.25 (DM)
FT_USB_D_P: J2.3 (D+), U3.1 (I/O1), U4.23 (DP)
FT_USB_SSRX_N: J2.8 (SSTX-), U3.7 (I/O5), U4.34 (RIDN)
FT_USB_SSRX_P: J2.9 (SSTX+), U3.8 (I/O6), U4.35 (RIDP)
FT_USB_SSTX_B_N: C59.2, U4.31 (TODN)
FT_USB_SSTX_B_P: C60.2, U4.32 (TODP)
FT_USB_SSTX_N: C59.1, J2.5 (SSRX-), U3.4 (I/O3)
FT_USB_SSTX_P: C60.1, J2.6 (SSRX+), U3.5 (I/O4)
GND: C48.2, C49.2, C50.2, C51.2, C52.2, C53.2, C54.2, C55.2, C56.2, C57.2, C58.2, C61.2, C62.2, C63.2, C64.2, C65.2, C66.2, C67.2, C68.2, C69.2, C70.2, C71.2, C73.2, C74.2, FB2.2, J2.4 (GND), J2.7 (DRAIN), R14.2, R16.2, U3.6 (GND), U4.1 (GND), U4.26 (GND), U4.29 (GND), U4.36 (GND), U4.77 (GND), Y1.2, Y1.4
unnamed: C48.1, FB2.1, J2.10 (SHIELD)
unnamed: R14.1, U4.27 (RREF)
unnamed: R15.1, R16.1, U4.37 (VBUS)
unnamed: R17.2, U4.10 (~SIWU)

Notes on the sheet:
CLOCK
FT601Q USB 3.0 interface
Power
USB-A Plug
anti ESD
FPGA-IO
