MillePoels/MurPhySDR/hardware/kicad/MurPhySDR.kicad_sch

## KiCad design hardware/kicad/MurPhySDR.kicad_sch (2024-05-19)

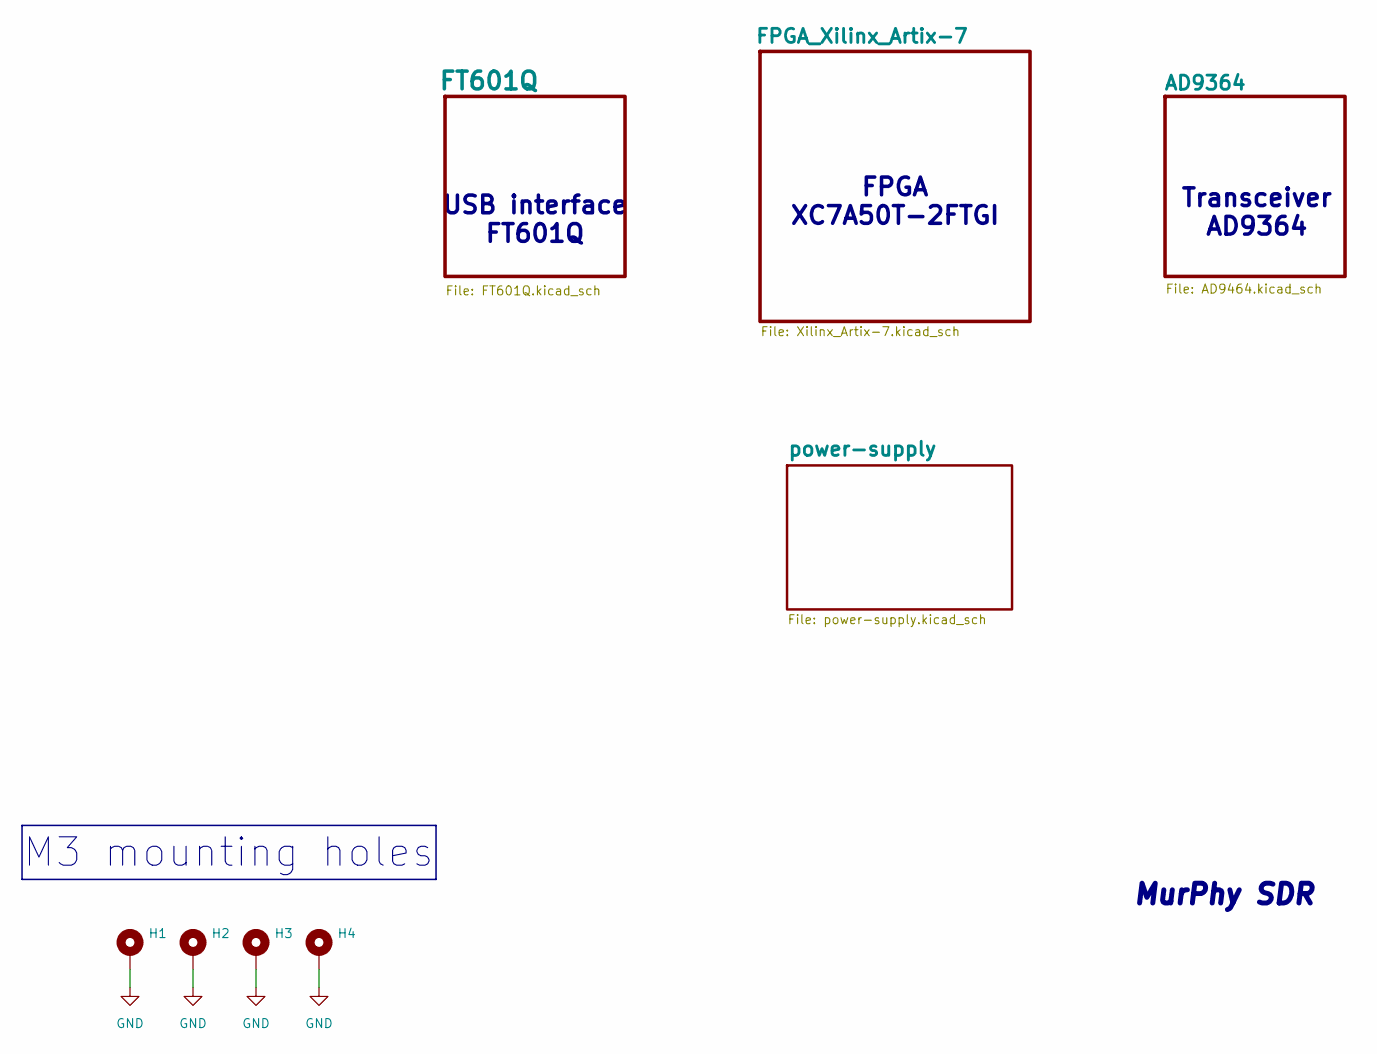
[picture p39: schematic MurPhySDR.kicad_sch]

Parts:
H1, H2, H3, H4: MountingHole_Pad; MountingHole_3.2mm_M3_Pad_Via; Manufacturer_Part_Number /

Connections:
GND: H1.1, H2.1, H3.1, H4.1

Notes on the sheet:
M3 mounting holes
MurPhy SDR
Transceiver AD9364
USB interface FT601Q
FPGA XC7A50T-2FTGI
