MillePoels/MurPhySDR/hardware/kicad/Xilinx_Artix-7_Banks.kicad_sch

## KiCad design hardware/kicad/Xilinx_Artix-7_Banks.kicad_sch (2024-05-19)

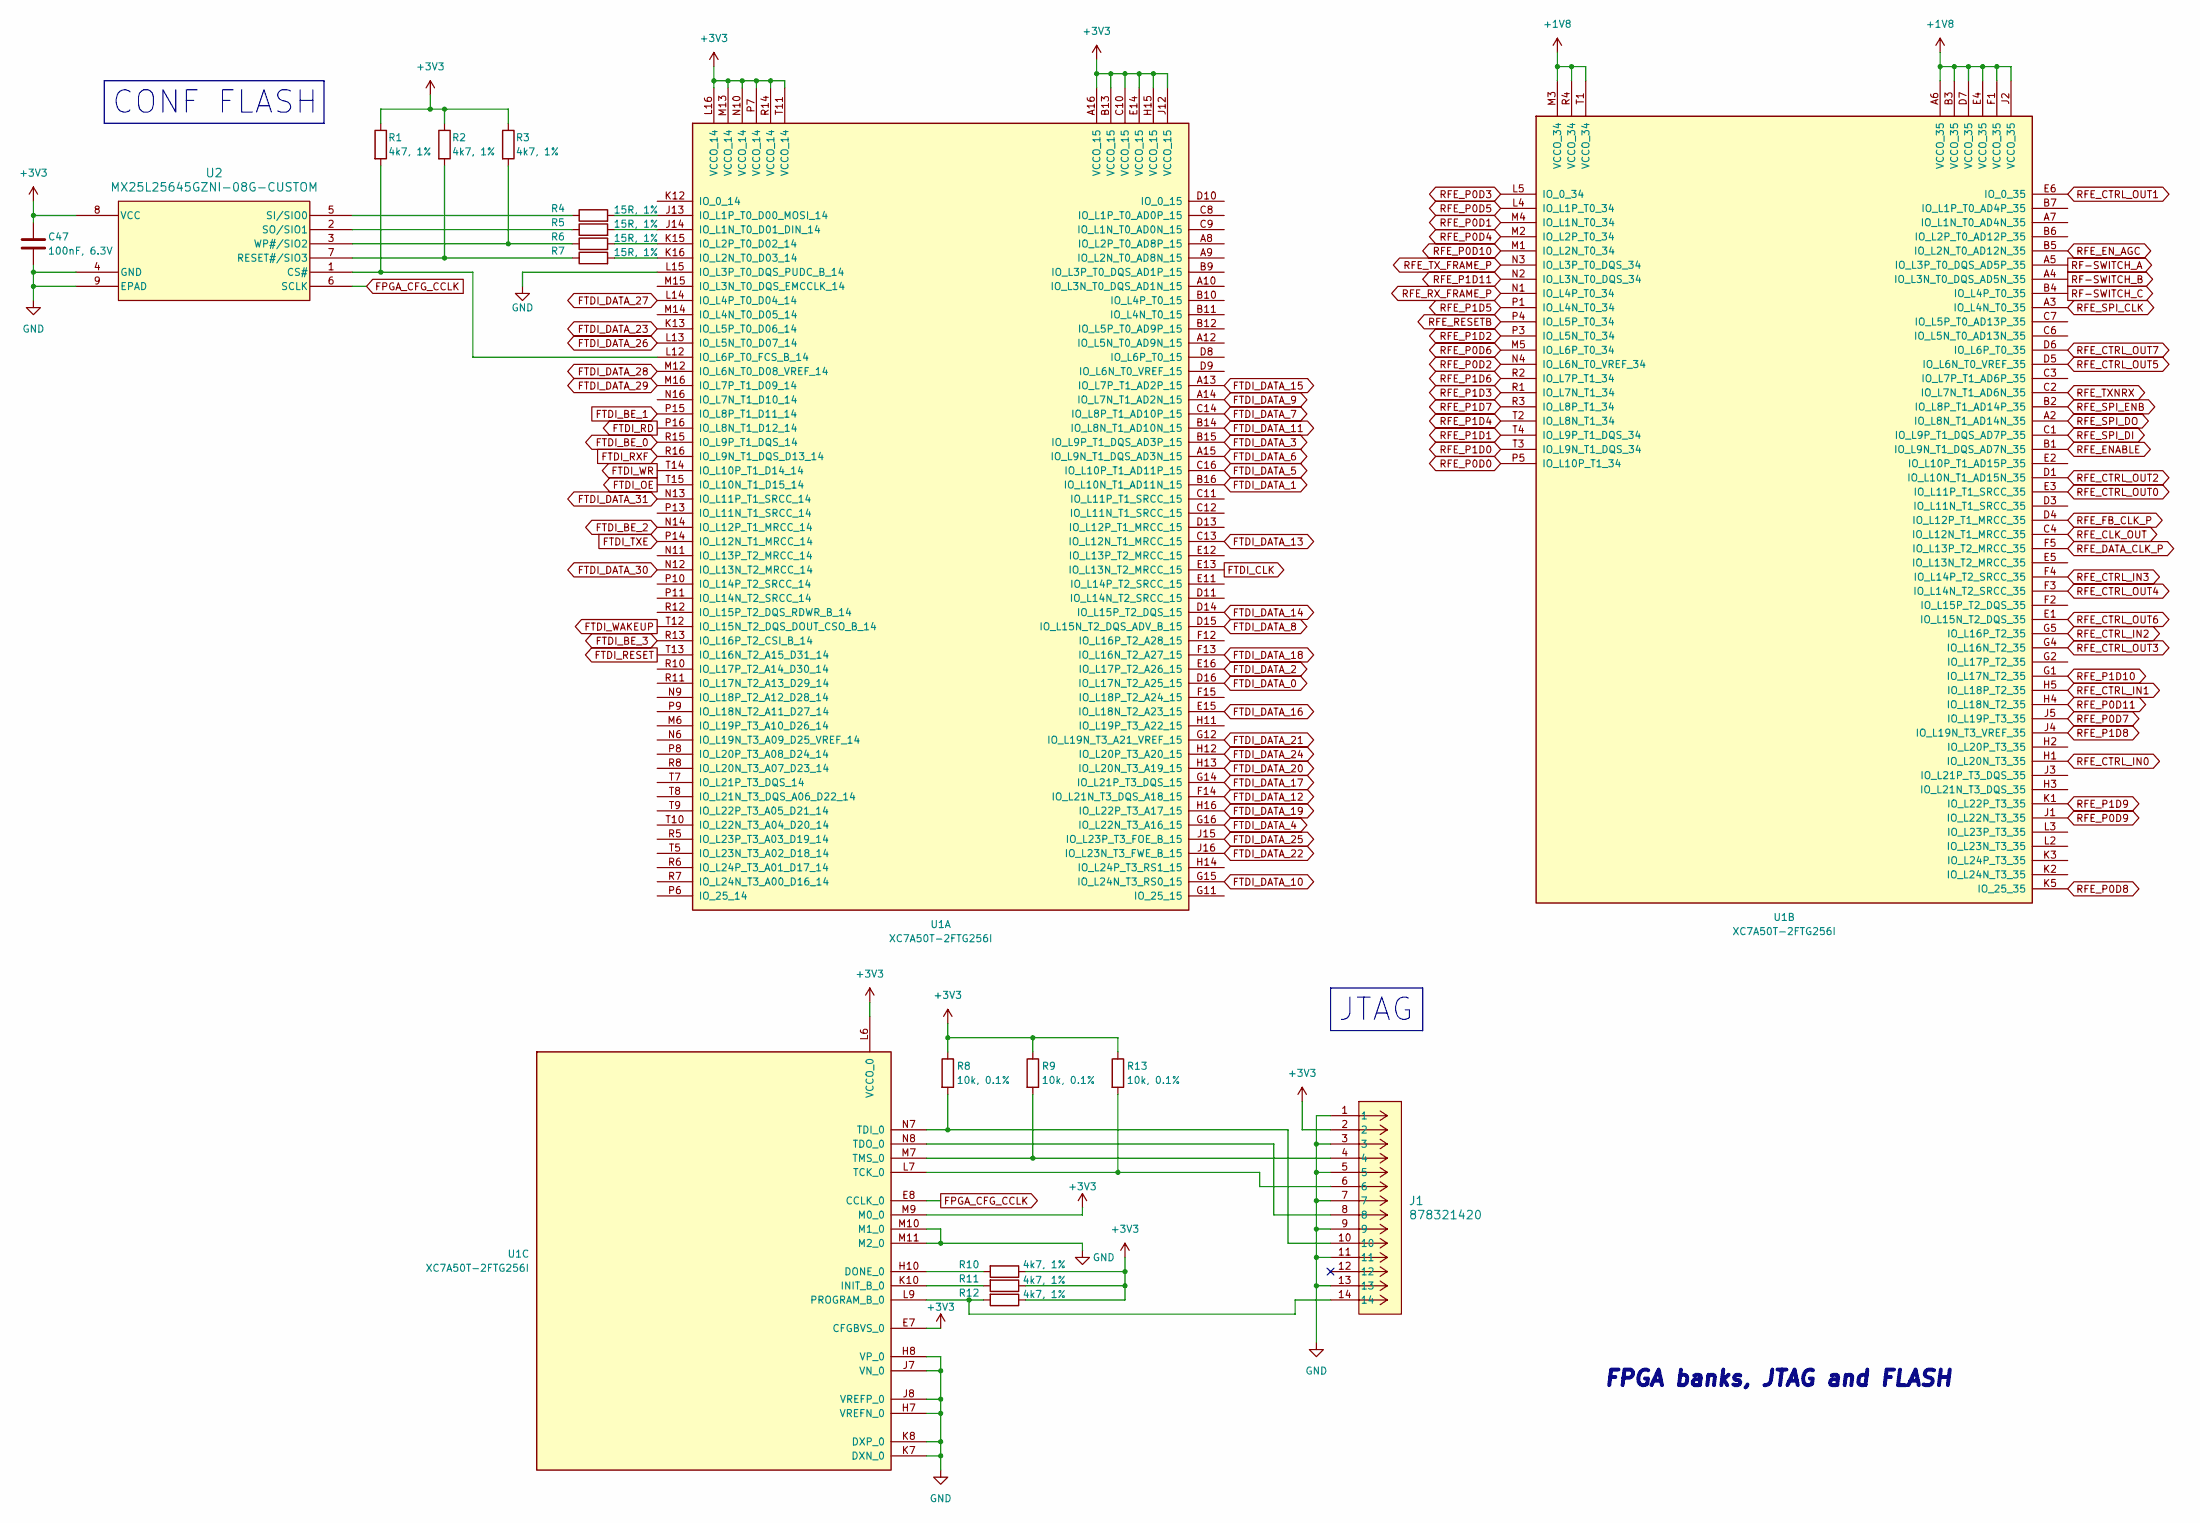
[picture p40: schematic Xilinx_Artix-7_Banks.kicad_sch]

Parts:
C47: 100nF, 6.3V; C_0201_0603Metric; Manufacturer_Part_Number GRM033R60J104KE19D; Mouser Part Number 81-GRM033R60J104KE19
J1: 878321420; CONN_87832-1420_MOL; Manufacturer_Part_Number 878321420; Mouser Part Number 538-87832-1420
R1, R2, R3, R10, R11, R12: 4k7, 1%; R_0402_1005Metric; Manufacturer_Part_Number RC0402FR-074K7L; Mouser Part Number 603-RC0402FR-074K7L
R4, R5, R6, R7: 15R, 1%; R_0201_0603Metric; Manufacturer_Part_Number RC0201FR-0715RL; Mouser Part Number 603-RC0201FR-0715RL
R8, R9, R13: 10k, 0.1%; R_0402_1005Metric; Manufacturer_Part_Number RT0402BRD0710KL; Mouser Part Number 603-RT0402BRD0710KL
U1: XC7A50T-2FTG256I; Xilinx_FTG256; Manufacturer_Part_Number XC7A50T-2FTG256I; Mouser Part Number 217-XC7A50T-2FTG256I
U2: MX25L25645GZNI-08G-CUSTOM; WSON8_6X5_MAC; Manufacturer_Part_Number MX25L25645GZNI-08G; Mouser Part Number /

Connections:
+1V8: U1.A6 (VCCO_35), U1.B3 (VCCO_35), U1.D7 (VCCO_35), U1.E4 (VCCO_35), U1.F1 (VCCO_35), U1.J2 (VCCO_35), U1.M3 (VCCO_34), U1.R4 (VCCO_34), U1.T1 (VCCO_34)
+3V3: C47.1, J1.2, R1.1, R2.1, R3.1, R8.1, R9.1, R10.1, R11.1, R12.1, R13.1, U1.A16 (VCCO_15), U1.B13 (VCCO_15), U1.C10 (VCCO_15), U1.E7 (CFGBVS_0), U1.E14 (VCCO_15), U1.H15 (VCCO_15), U1.J12 (VCCO_15), U1.L6 (VCCO_0), U1.L16 (VCCO_14), U1.M9 (M0_0), U1.M13 (VCCO_14), U1.N10 (VCCO_14), U1.P7 (VCCO_14), U1.R14 (VCCO_14), U1.T11 (VCCO_14), U2.8 (VCC)
FPGA_CFG_CCLK: U1.E8 (CCLK_0), U2.6 (SCLK)
FTDI_BE_0: U1.R15 (IO_L9P_T1_DQS_14)
FTDI_BE_1: U1.P15 (IO_L8P_T1_D11_14)
FTDI_BE_2: U1.N14 (IO_L12P_T1_MRCC_14)
FTDI_BE_3: U1.R13 (IO_L16P_T2_CSI_B_14)
FTDI_CLK: U1.E13 (IO_L13N_T2_MRCC_15)
FTDI_DATA_0: U1.D16 (IO_L17N_T2_A25_15)
FTDI_DATA_1: U1.B16 (IO_L10N_T1_AD11N_15)
FTDI_DATA_2: U1.E16 (IO_L17P_T2_A26_15)
FTDI_DATA_3: U1.B15 (IO_L9P_T1_DQS_AD3P_15)
FTDI_DATA_4: U1.G16 (IO_L22N_T3_A16_15)
FTDI_DATA_5: U1.C16 (IO_L10P_T1_AD11P_15)
FTDI_DATA_6: U1.A15 (IO_L9N_T1_DQS_AD3N_15)
FTDI_DATA_7: U1.C14 (IO_L8P_T1_AD10P_15)
FTDI_DATA_8: U1.D15 (IO_L15N_T2_DQS_ADV_B_15)
FTDI_DATA_9: U1.A14 (IO_L7N_T1_AD2N_15)
FTDI_DATA_10: U1.G15 (IO_L24N_T3_RS0_15)
FTDI_DATA_11: U1.B14 (IO_L8N_T1_AD10N_15)
FTDI_DATA_12: U1.F14 (IO_L21N_T3_DQS_A18_15)
FTDI_DATA_13: U1.C13 (IO_L12N_T1_MRCC_15)
FTDI_DATA_14: U1.D14 (IO_L15P_T2_DQS_15)
FTDI_DATA_15: U1.A13 (IO_L7P_T1_AD2P_15)
FTDI_DATA_16: U1.E15 (IO_L18N_T2_A23_15)
FTDI_DATA_17: U1.G14 (IO_L21P_T3_DQS_15)
FTDI_DATA_18: U1.F13 (IO_L16N_T2_A27_15)
FTDI_DATA_19: U1.H16 (IO_L22P_T3_A17_15)
FTDI_DATA_20: U1.H13 (IO_L20N_T3_A19_15)
FTDI_DATA_21: U1.G12 (IO_L19N_T3_A21_VREF_15)
FTDI_DATA_22: U1.J16 (IO_L23N_T3_FWE_B_15)
FTDI_DATA_23: U1.K13 (IO_L5P_T0_D06_14)
FTDI_DATA_24: U1.H12 (IO_L20P_T3_A20_15)
FTDI_DATA_25: U1.J15 (IO_L23P_T3_FOE_B_15)
FTDI_DATA_26: U1.L13 (IO_L5N_T0_D07_14)
FTDI_DATA_27: U1.L14 (IO_L4P_T0_D04_14)
FTDI_DATA_28: U1.M12 (IO_L6N_T0_D08_VREF_14)
FTDI_DATA_29: U1.M16 (IO_L7P_T1_D09_14)
FTDI_DATA_30: U1.N12 (IO_L13N_T2_MRCC_14)
FTDI_DATA_31: U1.N13 (IO_L11P_T1_SRCC_14)
FTDI_OE: U1.T15 (IO_L10N_T1_D15_14)
FTDI_RD: U1.P16 (IO_L8N_T1_D12_14)
FTDI_RESET: U1.T13 (IO_L16N_T2_A15_D31_14)
FTDI_RXF: U1.R16 (IO_L9N_T1_DQS_D13_14)
FTDI_TXE: U1.P14 (IO_L12N_T1_MRCC_14)
FTDI_WAKEUP: U1.T12 (IO_L15N_T2_DQS_DOUT_CSO_B_14)
FTDI_WR: U1.T14 (IO_L10P_T1_D14_14)
GND: C47.2, J1.1, J1.3, J1.5, J1.7, J1.9, J1.11, J1.13, U1.H7 (VREFN_0), U1.H8 (VP_0), U1.J7 (VN_0), U1.J8 (VREFP_0), U1.K7 (DXN_0), U1.K8 (DXP_0), U1.L15 (IO_L3P_T0_DQS_PUDC_B_14), U1.M10 (M1_0), U1.M11 (M2_0), U2.4 (GND), U2.9 (EPAD)
unnamed: J1.4, R9.2, U1.M7 (TMS_0)
unnamed: J1.6, R13.2, U1.L7 (TCK_0)
unnamed: J1.8, U1.N8 (TDO_0)
unnamed: J1.10, R8.2, U1.N7 (TDI_0)
unnamed: J1.14, R12.2, U1.L9 (PROGRAM_B_0)
unnamed: R1.2, U1.L12 (IO_L6P_T0_FCS_B_14), U2.1 (CS#)
unnamed: R2.2, R7.1, U2.7 (RESET#/SIO3)
unnamed: R3.2, R6.1, U2.3 (WP#/SIO2)
unnamed: R4.1, U2.5 (SI/SIO0)
unnamed: R4.2, U1.J13 (IO_L1P_T0_D00_MOSI_14)
unnamed: R5.1, U2.2 (SO/SIO1)
unnamed: R5.2, U1.J14 (IO_L1N_T0_D01_DIN_14)
unnamed: R6.2, U1.K15 (IO_L2P_T0_D02_14)
unnamed: R7.2, U1.K16 (IO_L2N_T0_D03_14)
unnamed: R10.2, U1.H10 (DONE_0)
unnamed: R11.2, U1.K10 (INIT_B_0)
RF-SWITCH_A: U1.A5 (IO_L3P_T0_DQS_AD5P_35)
RF-SWITCH_B: U1.A4 (IO_L3N_T0_DQS_AD5N_35)
RF-SWITCH_C: U1.B4 (IO_L4P_T0_35)
RFE_CLK_OUT: U1.C4 (IO_L12N_T1_MRCC_35)
RFE_CTRL_IN0: U1.H1 (IO_L20N_T3_35)
RFE_CTRL_IN1: U1.H5 (IO_L18P_T2_35)
RFE_CTRL_IN2: U1.G5 (IO_L16P_T2_35)
RFE_CTRL_IN3: U1.F4 (IO_L14P_T2_SRCC_35)
RFE_CTRL_OUT0: U1.E3 (IO_L11P_T1_SRCC_35)
RFE_CTRL_OUT1: U1.E6 (IO_0_35)
RFE_CTRL_OUT2: U1.D1 (IO_L10N_T1_AD15N_35)
RFE_CTRL_OUT3: U1.G4 (IO_L16N_T2_35)
RFE_CTRL_OUT4: U1.F3 (IO_L14N_T2_SRCC_35)
RFE_CTRL_OUT5: U1.D5 (IO_L6N_T0_VREF_35)
RFE_CTRL_OUT6: U1.E1 (IO_L15N_T2_DQS_35)
RFE_CTRL_OUT7: U1.D6 (IO_L6P_T0_35)
RFE_DATA_CLK_P: U1.F5 (IO_L13P_T2_MRCC_35)
RFE_ENABLE: U1.B1 (IO_L9N_T1_DQS_AD7N_35)
RFE_EN_AGC: U1.B5 (IO_L2N_T0_AD12N_35)
RFE_FB_CLK_P: U1.D4 (IO_L12P_T1_MRCC_35)
RFE_P0D0: U1.P5 (IO_L10P_T1_34)
RFE_P0D1: U1.M4 (IO_L1N_T0_34)
RFE_P0D2: U1.N4 (IO_L6N_T0_VREF_34)
RFE_P0D3: U1.L5 (IO_0_34)
RFE_P0D4: U1.M2 (IO_L2P_T0_34)
RFE_P0D5: U1.L4 (IO_L1P_T0_34)
RFE_P0D6: U1.M5 (IO_L6P_T0_34)
RFE_P0D7: U1.J5 (IO_L19P_T3_35)
RFE_P0D8: U1.K5 (IO_25_35)
RFE_P0D9: U1.J1 (IO_L22N_T3_35)
RFE_P0D10: U1.M1 (IO_L2N_T0_34)
RFE_P0D11: U1.H4 (IO_L18N_T2_35)
RFE_P1D0: U1.T3 (IO_L9N_T1_DQS_34)
RFE_P1D1: U1.T4 (IO_L9P_T1_DQS_34)
RFE_P1D2: U1.P3 (IO_L5N_T0_34)
RFE_P1D3: U1.R1 (IO_L7N_T1_34)
RFE_P1D4: U1.T2 (IO_L8N_T1_34)
RFE_P1D5: U1.P1 (IO_L4N_T0_34)
RFE_P1D6: U1.R2 (IO_L7P_T1_34)
RFE_P1D7: U1.R3 (IO_L8P_T1_34)
RFE_P1D8: U1.J4 (IO_L19N_T3_VREF_35)
RFE_P1D9: U1.K1 (IO_L22P_T3_35)
RFE_P1D10: U1.G1 (IO_L17N_T2_35)
RFE_P1D11: U1.N2 (IO_L3N_T0_DQS_34)
RFE_RESETB: U1.P4 (IO_L5P_T0_34)
RFE_RX_FRAME_P: U1.N1 (IO_L4P_T0_34)
RFE_SPI_CLK: U1.A3 (IO_L4N_T0_35)
RFE_SPI_DI: U1.C1 (IO_L9P_T1_DQS_AD7P_35)
RFE_SPI_DO: U1.A2 (IO_L8N_T1_AD14N_35)
RFE_SPI_ENB: U1.B2 (IO_L8P_T1_AD14P_35)
RFE_TXNRX: U1.C2 (IO_L7N_T1_AD6N_35)
RFE_TX_FRAME_P: U1.N3 (IO_L3P_T0_DQS_34)

Notes on the sheet:
FPGA banks, JTAG and FLASH
JTAG
CONF FLASH
