MillePoels/MurPhySDR/hardware/kicad/Xilinx_Artix-7_power-supply.kicad_sch

## KiCad design hardware/kicad/Xilinx_Artix-7_power-supply.kicad_sch (2024-05-19)

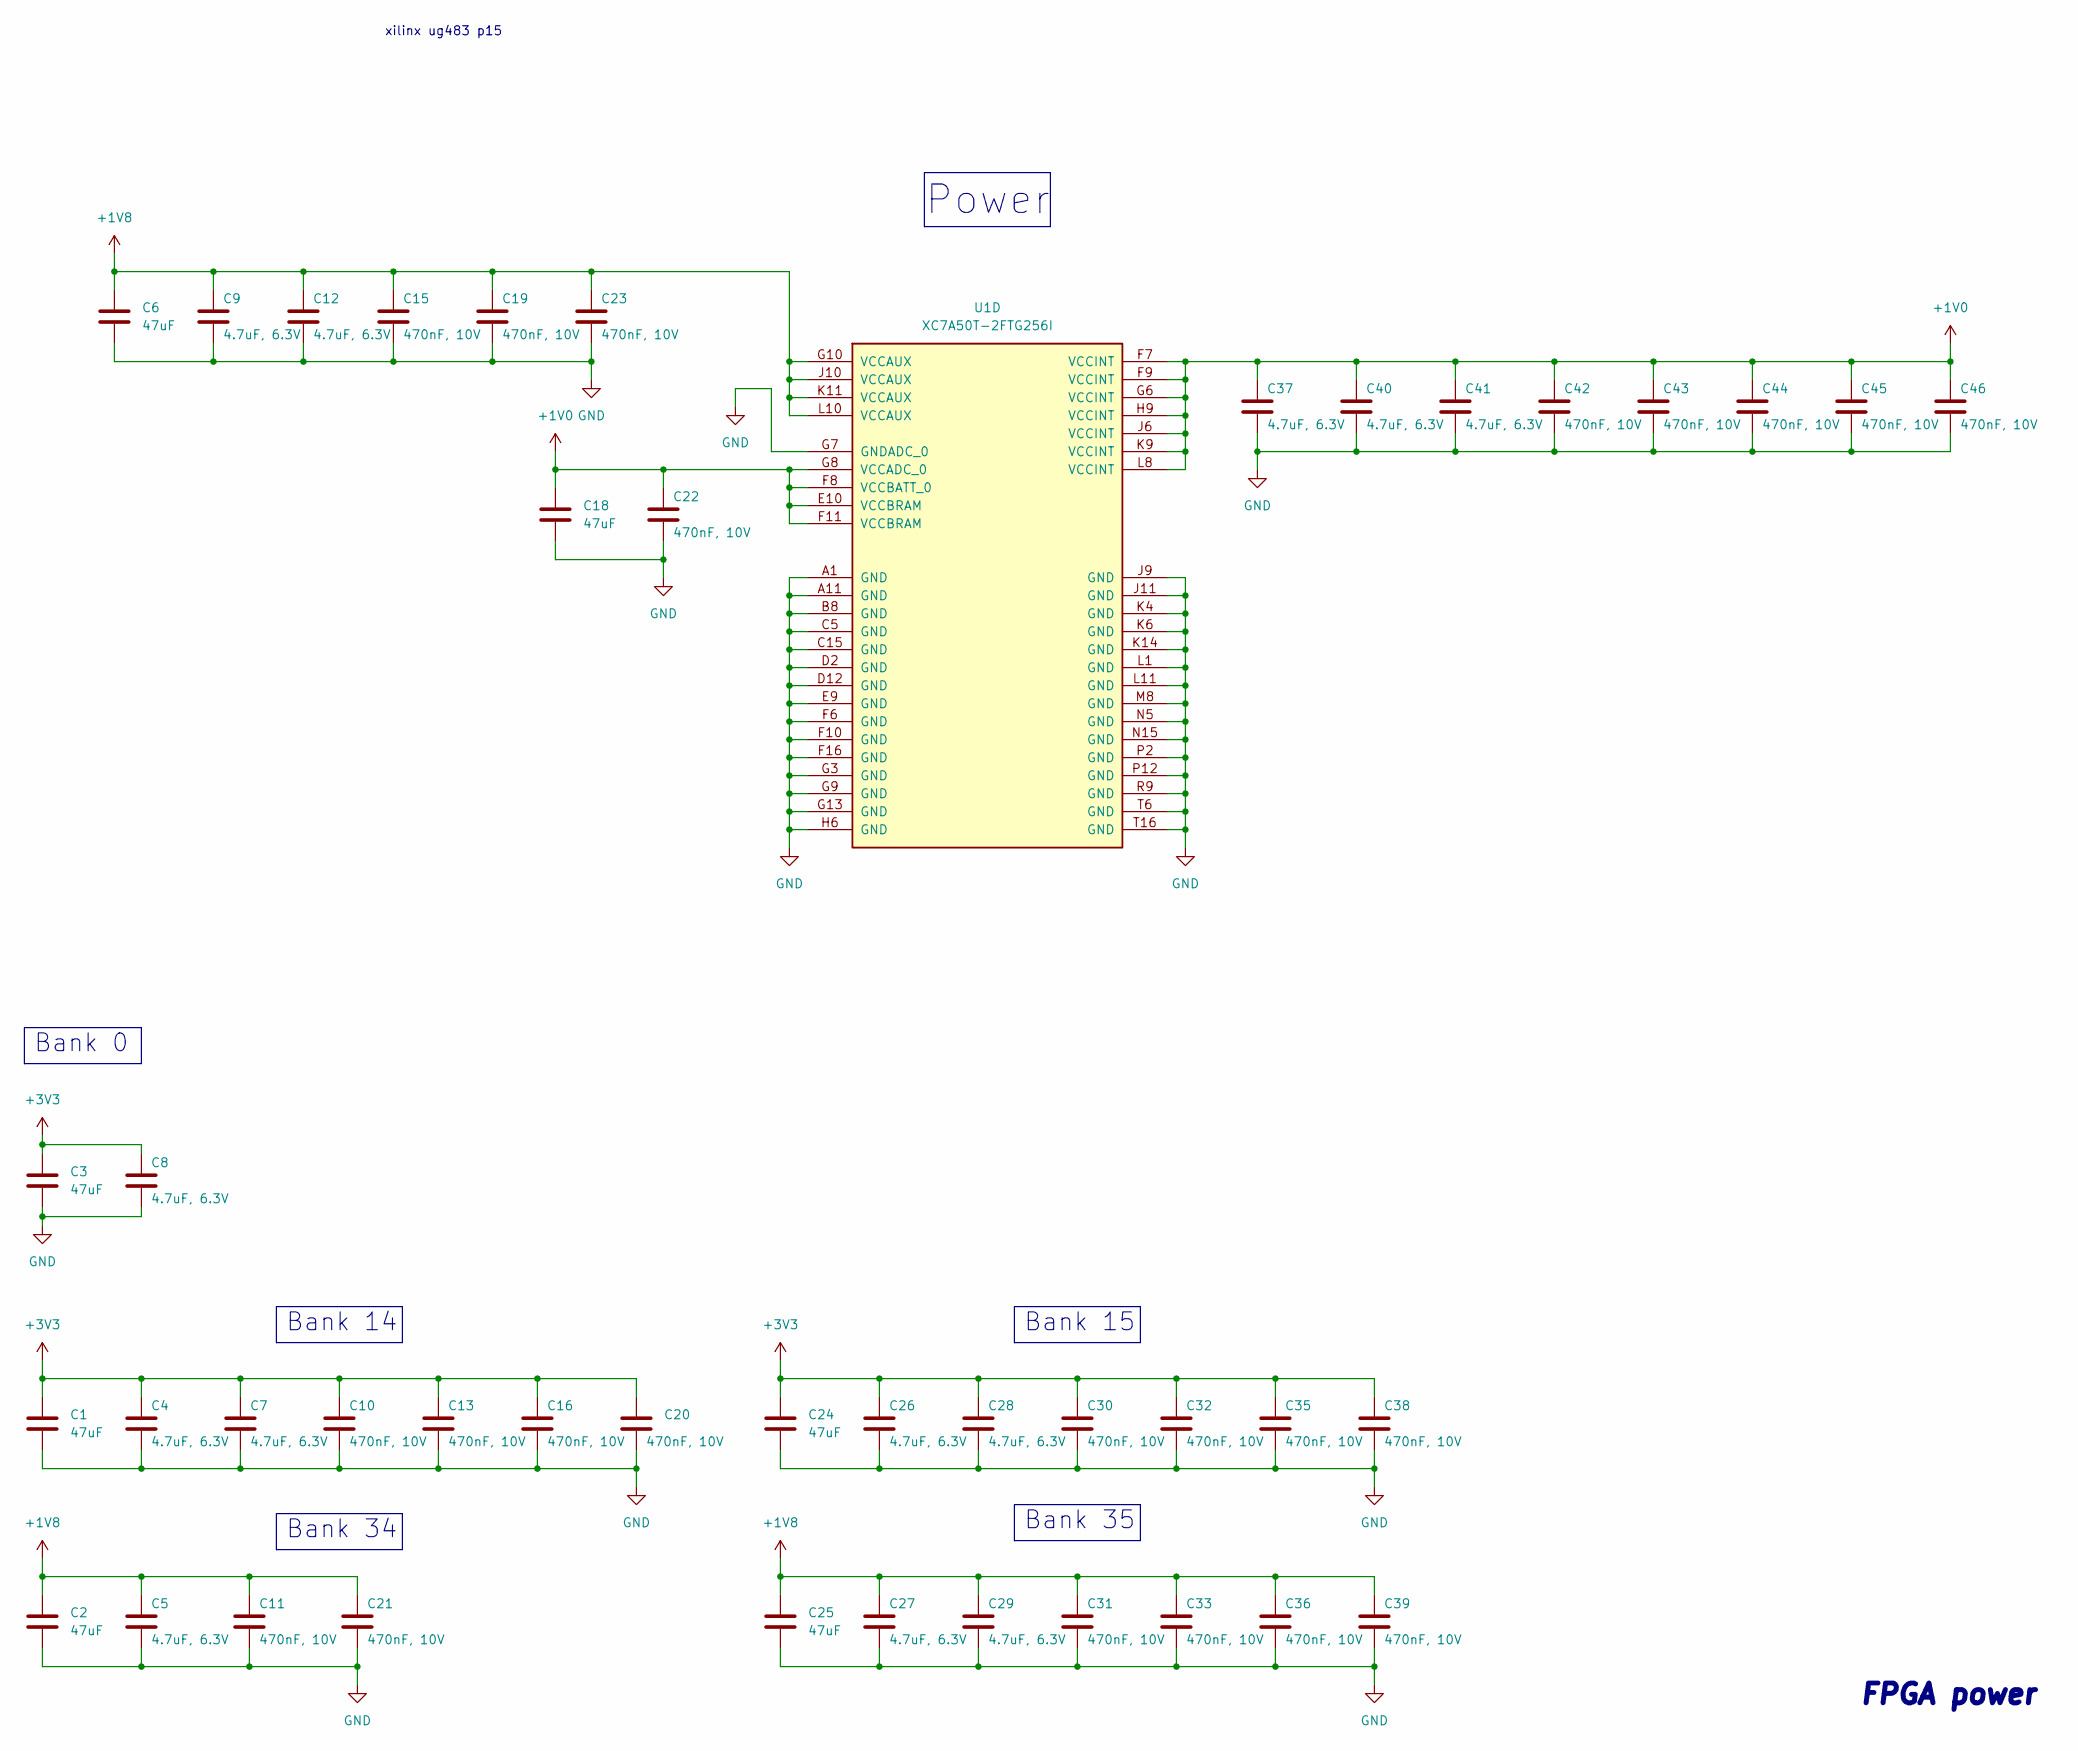
[picture p41: schematic Xilinx_Artix-7_power-supply.kicad_sch]

Parts:
C1, C2, C3, C6, C18, C24, C25: 47uF; C_1210_3225Metric; Manufacturer_Part_Number GRM32ER71A476KE15L; Mouser Part Number 81-GRM32ER71A476KE5L
C4, C5, C7, C8, C9, C12, C26, C27, C28, C29, C37, C40, C41: 4.7uF, 6.3V; C_0402_1005Metric; Manufacturer_Part_Number GRM155R60J475ME87D; Mouser Part Number 81-GRM155R60J475ME8D
C10, C11, C13, C15, C16, C19, C20, C21, C22, C23, C30, C31, C32, C33, C35, C36, C38, C39, C42, C43, C44, C45, C46: 470nF, 10V; C_0402_1005Metric; Manufacturer_Part_Number GRM155R61A474KE15D; Mouser Part Number 81-GRM155R61A474KE5D
U1: XC7A50T-2FTG256I; Xilinx_FTG256; Manufacturer_Part_Number XC7A50T-2FTG256I; Mouser Part Number 217-XC7A50T-2FTG256I

Connections:
+1V0: C18.1, C22.1, C37.1, C40.1, C41.1, C42.1, C43.1, C44.1, C45.1, C46.1, U1.E10 (VCCBRAM), U1.F7 (VCCINT), U1.F8 (VCCBATT_0), U1.F9 (VCCINT), U1.F11 (VCCBRAM), U1.G6 (VCCINT), U1.G8 (VCCADC_0), U1.H9 (VCCINT), U1.J6 (VCCINT), U1.K9 (VCCINT), U1.L8 (VCCINT)
+1V8: C2.1, C5.1, C6.1, C9.1, C11.1, C12.1, C15.1, C19.1, C21.1, C23.1, C25.1, C27.1, C29.1, C31.1, C33.1, C36.1, C39.1, U1.G10 (VCCAUX), U1.J10 (VCCAUX), U1.K11 (VCCAUX), U1.L10 (VCCAUX)
+3V3: C1.1, C3.1, C4.1, C7.1, C8.1, C10.1, C13.1, C16.1, C20.1, C24.1, C26.1, C28.1, C30.1, C32.1, C35.1, C38.1
GND: C1.2, C2.2, C3.2, C4.2, C5.2, C6.2, C7.2, C8.2, C9.2, C10.2, C11.2, C12.2, C13.2, C15.2, C16.2, C18.2, C19.2, C20.2, C21.2, C22.2, C23.2, C24.2, C25.2, C26.2, C27.2, C28.2, C29.2, C30.2, C31.2, C32.2, C33.2, C35.2, C36.2, C37.2, C38.2, C39.2, C40.2, C41.2, C42.2, C43.2, C44.2, C45.2, C46.2, U1.A1 (GND), U1.A11 (GND), U1.B8 (GND), U1.C5 (GND), U1.C15 (GND), U1.D2 (GND), U1.D12 (GND), U1.E9 (GND), U1.F6 (GND), U1.F10 (GND), U1.F16 (GND), U1.G3 (GND), U1.G7 (GNDADC_0), U1.G9 (GND), U1.G13 (GND), U1.H6 (GND), U1.J9 (GND), U1.J11 (GND), U1.K4 (GND), U1.K6 (GND), U1.K14 (GND), U1.L1 (GND), U1.L11 (GND), U1.M8 (GND), U1.N5 (GND), U1.N15 (GND), U1.P2 (GND), U1.P12 (GND), U1.R9 (GND), U1.T6 (GND), U1.T16 (GND)

Notes on the sheet:
Bank 0
Power
Bank 14
Bank 35
Bank 15
Bank 34
xilinx ug483 p15
FPGA power
