MillePoels/MurPhySDR/hardware/kicad/power-supply.kicad_sch

## KiCad design hardware/kicad/power-supply.kicad_sch (2024-05-19)

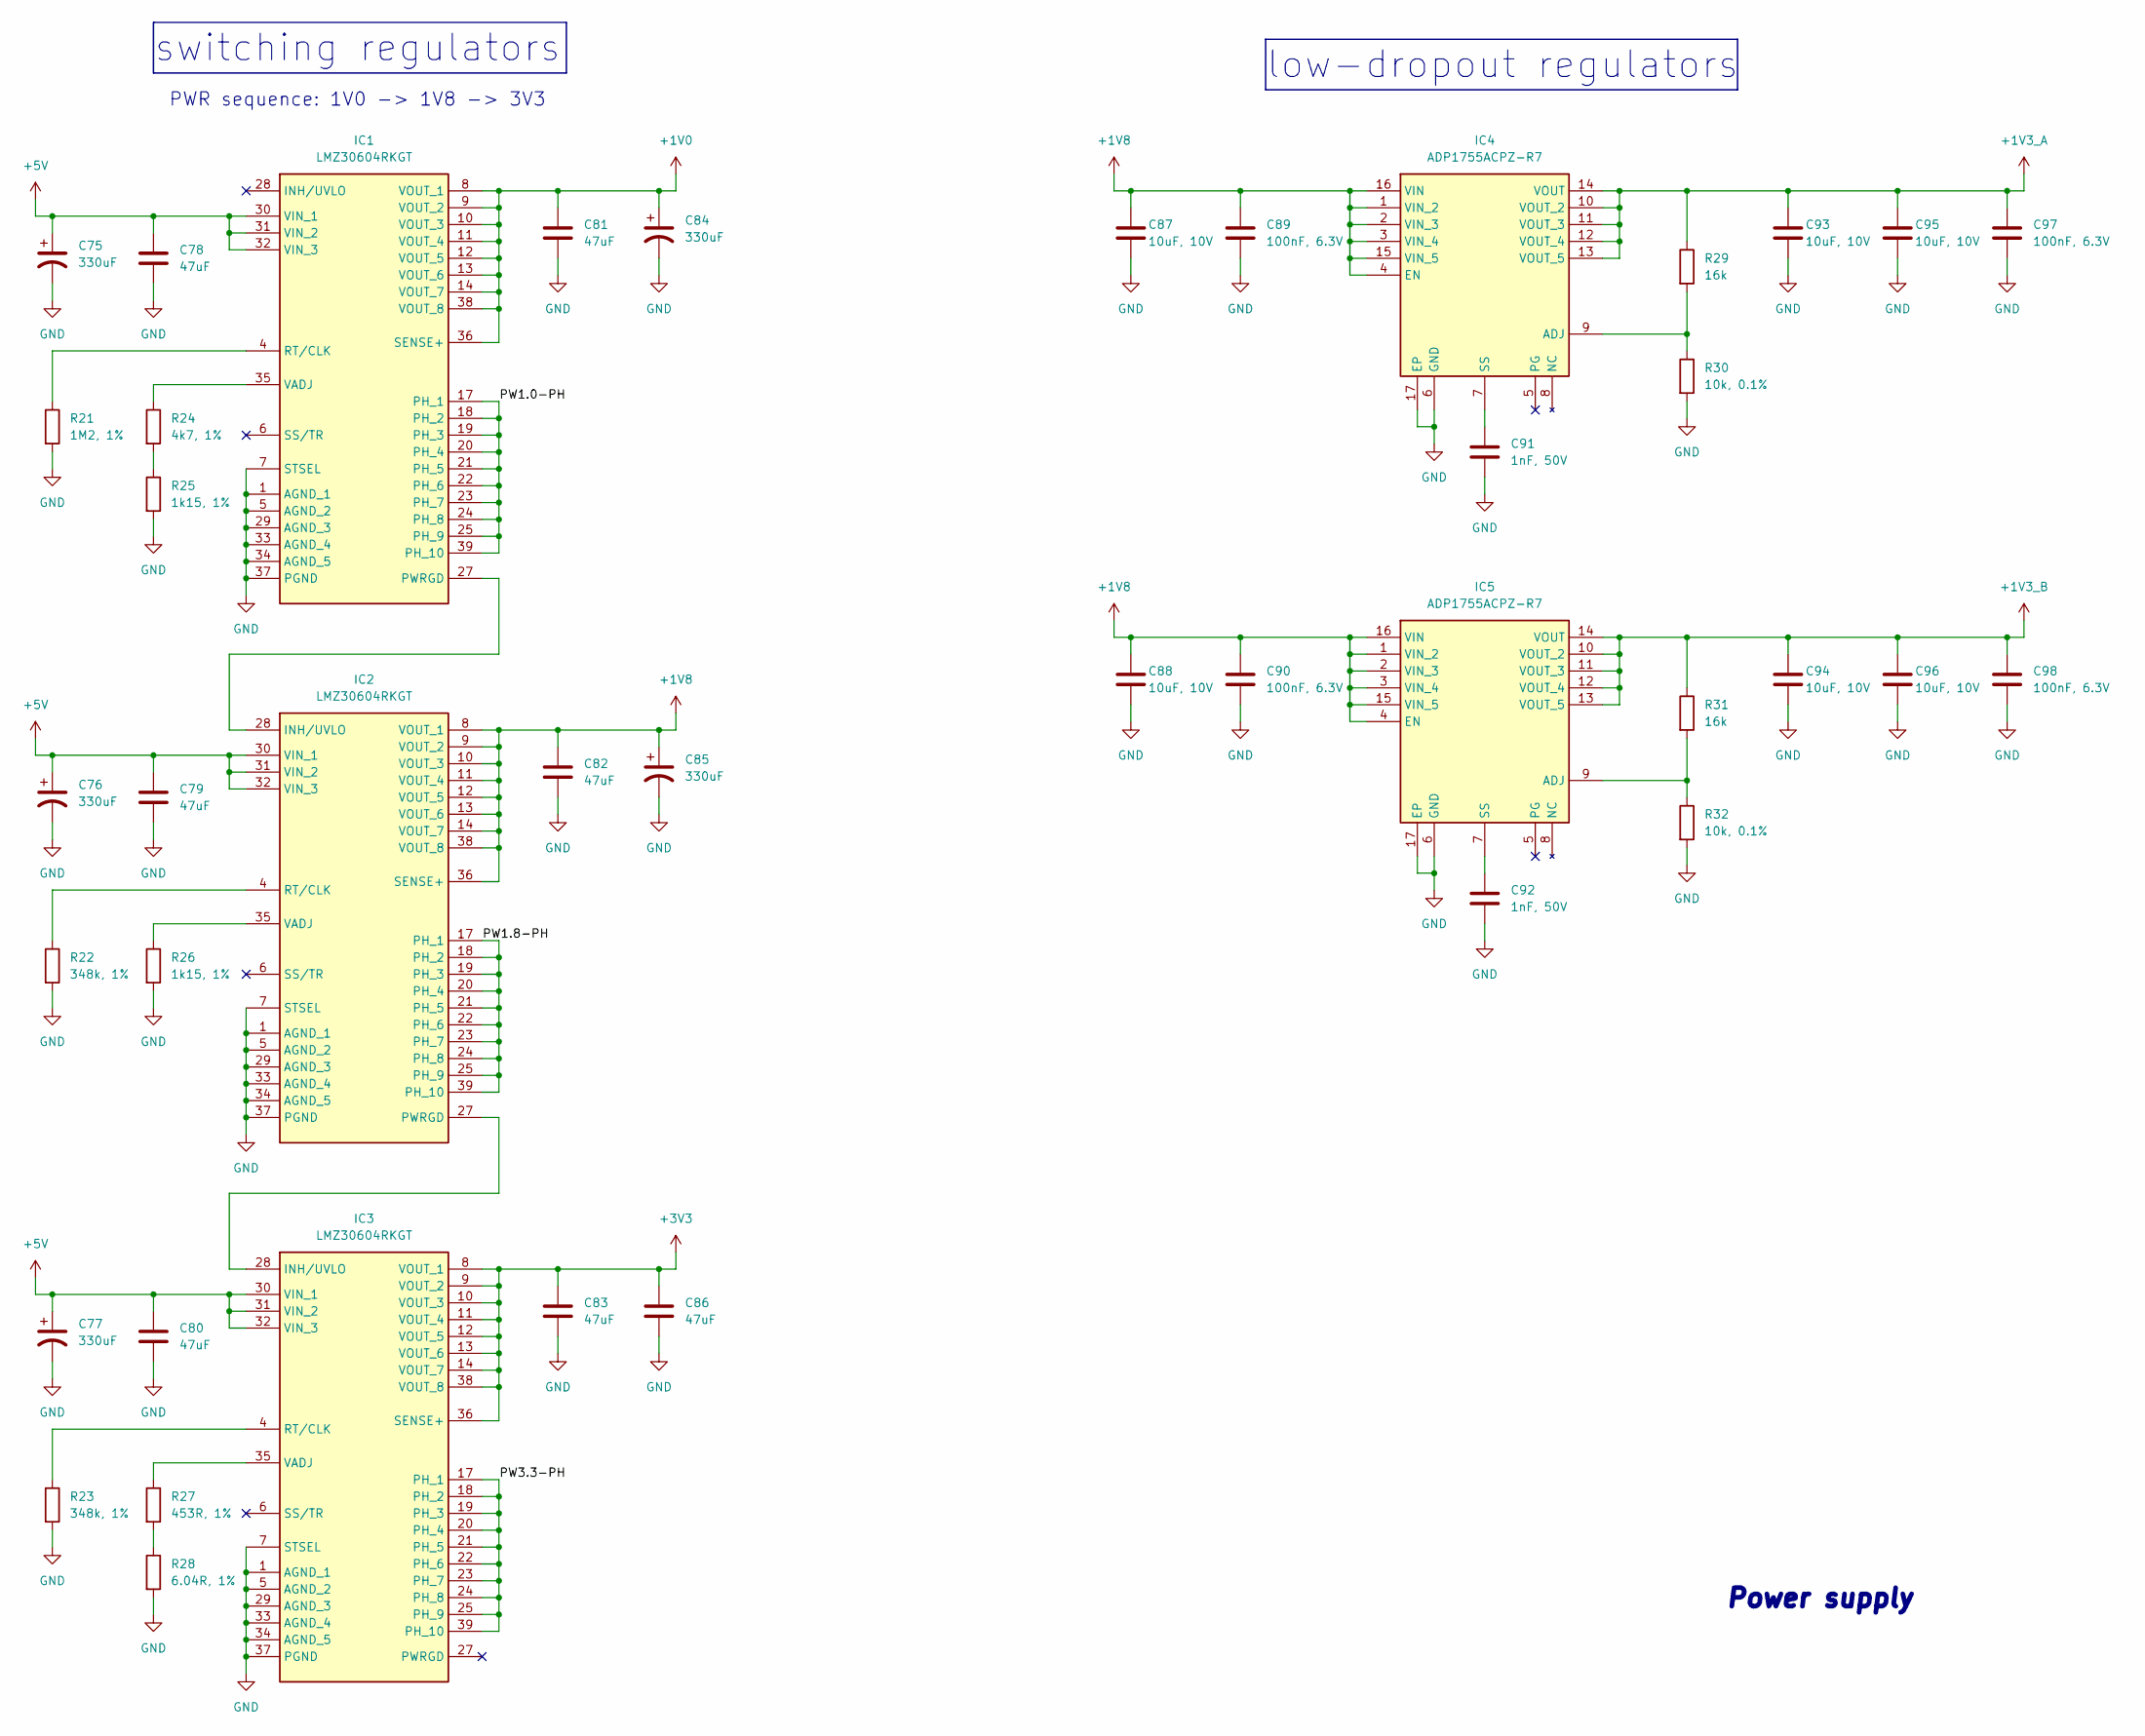
[picture p42: schematic power-supply.kicad_sch]

Parts:
C75, C76, C77, C84, C85: 330uF; 6TPE330MFL; Manufacturer_Part_Number 6TPE330MFL; Mouser Part Number 667-6TPE330MFL
C78, C79, C80, C81, C82, C83, C86: 47uF; C_1210_3225Metric; Manufacturer_Part_Number GRM32ER71A476KE15L; Mouser Part Number 81-GRM32ER71A476KE5L
C87, C88, C93, C94, C95, C96: 10uF, 10V; C_0603_1608Metric; Manufacturer_Part_Number GRM188R61A106ME69D; Mouser Part Number 81-GRM188R61A106ME9D
C89, C90, C97, C98: 100nF, 6.3V; C_0201_0603Metric; Manufacturer_Part_Number GRM033R60J104KE19D; Mouser Part Number 81-GRM033R60J104KE19
C91, C92: 1nF, 50V; C_0201_0603Metric; Manufacturer_Part_Number GRM0335C1H102JE01D; Mouser Part Number 81-GRM0335C1H102JE1D
IC1, IC2, IC3: LMZ30604RKGT; Mouser Part Number 595-LMZ30604RKGT
IC4, IC5: ADP1755ACPZ-R7; QFN65P400X400X100-17N; Mouser Part Number 584-ADP1755ACPZ-R7
R21: 1M2, 1%; R_0402_1005Metric; Manufacturer_Part_Number AC0402FR-071M2L; Mouser Part Number 603-AC0402FR-071M2L
R22, R23: 348k, 1%; R_0402_1005Metric; Manufacturer_Part_Number RC0402FR-07348KL; Mouser Part Number 603-RC0402FR-07348KL
R24: 4k7, 1%; R_0402_1005Metric; Manufacturer_Part_Number RC0402FR-074K7L; Mouser Part Number 603-RC0402FR-074K7L
R25, R26: 1k15, 1%; R_0402_1005Metric; Manufacturer_Part_Number RC0402FR-071K15L; Mouser Part Number 603-RC0402FR-071K15L
R27: 453R, 1%; R_0402_1005Metric; Manufacturer_Part_Number RC0402FR-07453RL; Mouser Part Number 603-RC0402FR-07453RL
R28: 6.04R, 1%; R_0402_1005Metric; Manufacturer_Part_Number RC0402FR-076R04L; Mouser Part Number 603-RC0402FR-076R04L
R29, R31: 16k; R_0402_1005Metric; Manufacturer_Part_Number RC0402FR-0716KL; Mouser Part Number 603-RC0402FR-0716KL
R30, R32: 10k, 0.1%; R_0402_1005Metric; Manufacturer_Part_Number RT0402BRD0710KL; Mouser Part Number 603-RT0402BRD0710KL

Connections:
+1V0: C81.1, C84.1, IC1.8 (VOUT_1), IC1.9 (VOUT_2), IC1.10 (VOUT_3), IC1.11 (VOUT_4), IC1.12 (VOUT_5), IC1.13 (VOUT_6), IC1.14 (VOUT_7), IC1.36 (SENSE+), IC1.38 (VOUT_8)
+1V3_A: C93.1, C95.1, C97.1, IC4.10 (VOUT_2), IC4.11 (VOUT_3), IC4.12 (VOUT_4), IC4.13 (VOUT_5), IC4.14 (VOUT), R29.1
+1V3_B: C94.1, C96.1, C98.1, IC5.10 (VOUT_2), IC5.11 (VOUT_3), IC5.12 (VOUT_4), IC5.13 (VOUT_5), IC5.14 (VOUT), R31.1
+1V8: C82.1, C85.1, C87.1, C88.1, C89.1, C90.1, IC2.8 (VOUT_1), IC2.9 (VOUT_2), IC2.10 (VOUT_3), IC2.11 (VOUT_4), IC2.12 (VOUT_5), IC2.13 (VOUT_6), IC2.14 (VOUT_7), IC2.36 (SENSE+), IC2.38 (VOUT_8), IC4.1 (VIN_2), IC4.2 (VIN_3), IC4.3 (VIN_4), IC4.4 (EN), IC4.15 (VIN_5), IC4.16 (VIN), IC5.1 (VIN_2), IC5.2 (VIN_3), IC5.3 (VIN_4), IC5.4 (EN), IC5.15 (VIN_5), IC5.16 (VIN)
+3V3: C83.1, C86.1, IC3.8 (VOUT_1), IC3.9 (VOUT_2), IC3.10 (VOUT_3), IC3.11 (VOUT_4), IC3.12 (VOUT_5), IC3.13 (VOUT_6), IC3.14 (VOUT_7), IC3.36 (SENSE+), IC3.38 (VOUT_8)
+5V: C75.1, C76.1, C77.1, C78.1, C79.1, C80.1, IC1.30 (VIN_1), IC1.31 (VIN_2), IC1.32 (VIN_3), IC2.30 (VIN_1), IC2.31 (VIN_2), IC2.32 (VIN_3), IC3.30 (VIN_1), IC3.31 (VIN_2), IC3.32 (VIN_3)
GND: C75.2, C76.2, C77.2, C78.2, C79.2, C80.2, C81.2, C82.2, C83.2, C84.2, C85.2, C86.2, C87.2, C88.2, C89.2, C90.2, C91.2, C92.2, C93.2, C94.2, C95.2, C96.2, C97.2, C98.2, IC1.1 (AGND_1), IC1.5 (AGND_2), IC1.7 (STSEL), IC1.29 (AGND_3), IC1.33 (AGND_4), IC1.34 (AGND_5), IC1.37 (PGND), IC2.1 (AGND_1), IC2.5 (AGND_2), IC2.7 (STSEL), IC2.29 (AGND_3), IC2.33 (AGND_4), IC2.34 (AGND_5), IC2.37 (PGND), IC3.1 (AGND_1), IC3.5 (AGND_2), IC3.7 (STSEL), IC3.29 (AGND_3), IC3.33 (AGND_4), IC3.34 (AGND_5), IC3.37 (PGND), IC4.6 (GND), IC4.17 (EP), IC5.6 (GND), IC5.17 (EP), R21.2, R22.2, R23.2, R25.2, R26.2, R28.2, R30.2, R32.2
unnamed: C91.1, IC4.7 (SS)
unnamed: C92.1, IC5.7 (SS)
unnamed: IC1.4 (RT/CLK), R21.1
unnamed: IC1.27 (PWRGD), IC2.28 (INH/UVLO)
unnamed: IC1.35 (VADJ), R24.1
unnamed: IC2.4 (RT/CLK), R22.1
unnamed: IC2.27 (PWRGD), IC3.28 (INH/UVLO)
unnamed: IC2.35 (VADJ), R26.1
unnamed: IC3.4 (RT/CLK), R23.1
unnamed: IC3.35 (VADJ), R27.1
unnamed: IC4.9 (ADJ), R29.2, R30.1
unnamed: IC5.9 (ADJ), R31.2, R32.1
unnamed: R24.2, R25.1
unnamed: R27.2, R28.1
PW1.0-PH: IC1.17 (PH_1), IC1.18 (PH_2), IC1.19 (PH_3), IC1.20 (PH_4), IC1.21 (PH_5), IC1.22 (PH_6), IC1.23 (PH_7), IC1.24 (PH_8), IC1.25 (PH_9), IC1.39 (PH_10)
PW1.8-PH: IC2.17 (PH_1), IC2.18 (PH_2), IC2.19 (PH_3), IC2.20 (PH_4), IC2.21 (PH_5), IC2.22 (PH_6), IC2.23 (PH_7), IC2.24 (PH_8), IC2.25 (PH_9), IC2.39 (PH_10)
PW3.3-PH: IC3.17 (PH_1), IC3.18 (PH_2), IC3.19 (PH_3), IC3.20 (PH_4), IC3.21 (PH_5), IC3.22 (PH_6), IC3.23 (PH_7), IC3.24 (PH_8), IC3.25 (PH_9), IC3.39 (PH_10)

Notes on the sheet:
Power supply
switching regulators
low-dropout regulators
PWR sequence: 1V0 -> 1V8 -> 3V3
